gtips/reviung/reviung53/acrylic-plate/for-stacked-acrylic-case/README.md

# Stacked acrylic case  
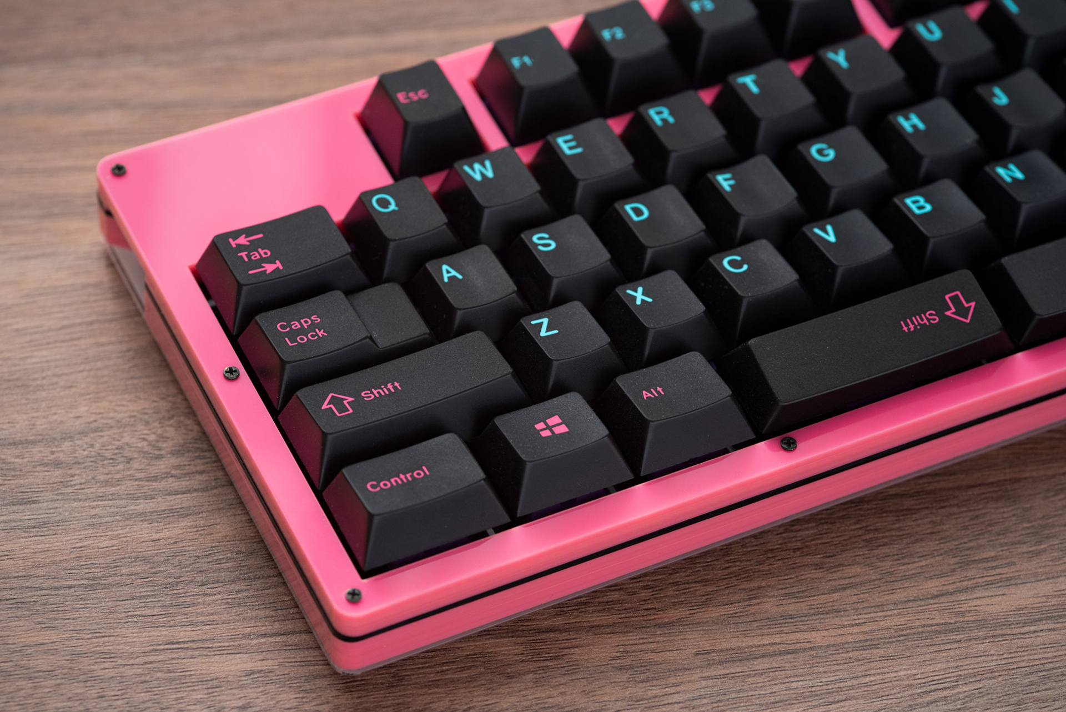
[picture p38: reviung53/image/reviung53-07.jpg]
REVIUNG53
  
  
Stacked acrylic cases.  
Includes Hi-Pro frame.  
  
Cut out the outer frame of the main PCB and install it.  
  
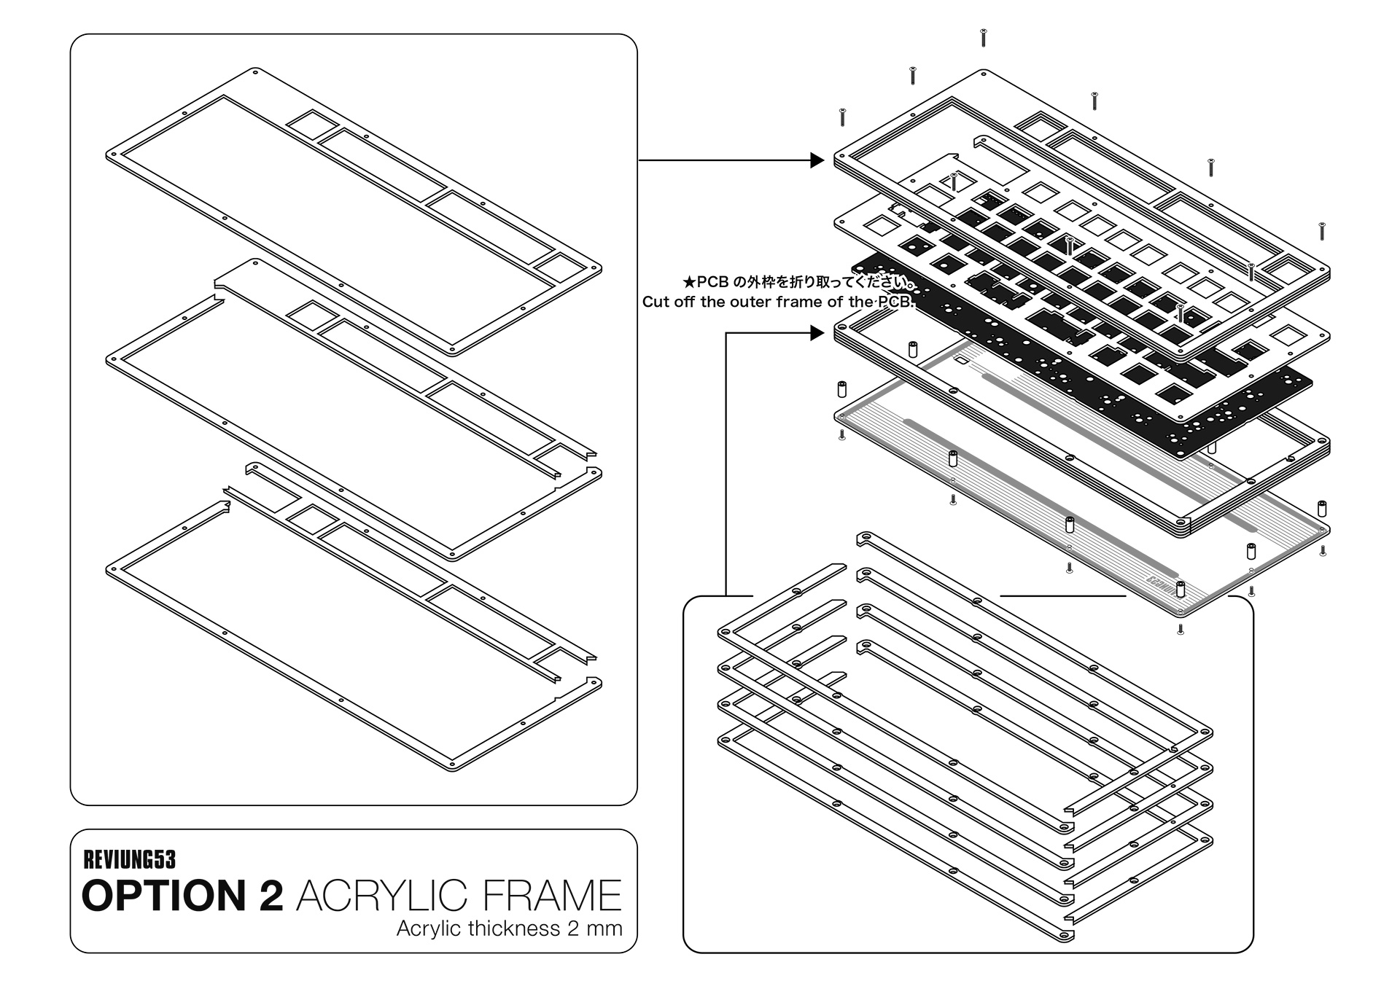
[picture p39: reviung53/acrylic-plate/for-stacked-acrylic-case/Assembly_drawing.jpg]
REVIUNG53
