gtips/reviung/reviung53/acrylic-plate/mcu-cover-ver1.0/README.md

# MCU cover  
Use this cover if you are not using the Hi-Pro frame.  

If the ProMicro pin headers come in contact, attach them with a 2 or 3mm spacer in between.
