gtips/reviung/reviung41/acrylic-plate/bottom-plate/README.md

# reviung41 bottom-plate  

Acrylic thickness is 2mm  
  
Width 253.34 mm  
Height 107.073 mm
