gtips/reviung/reviung41/acrylic-plate/top-plate/README.md

# reviung41 top-plate  

Acrylic thickness is 2mm  
  
Width 253.34 mm  
Height 101.157mm
