gtips/reviung/reviung41/acrylic-plate/lower-middle-plate/README.md

# reviung41 lower-middle-plate  

Acrylic thickness is 3mm  

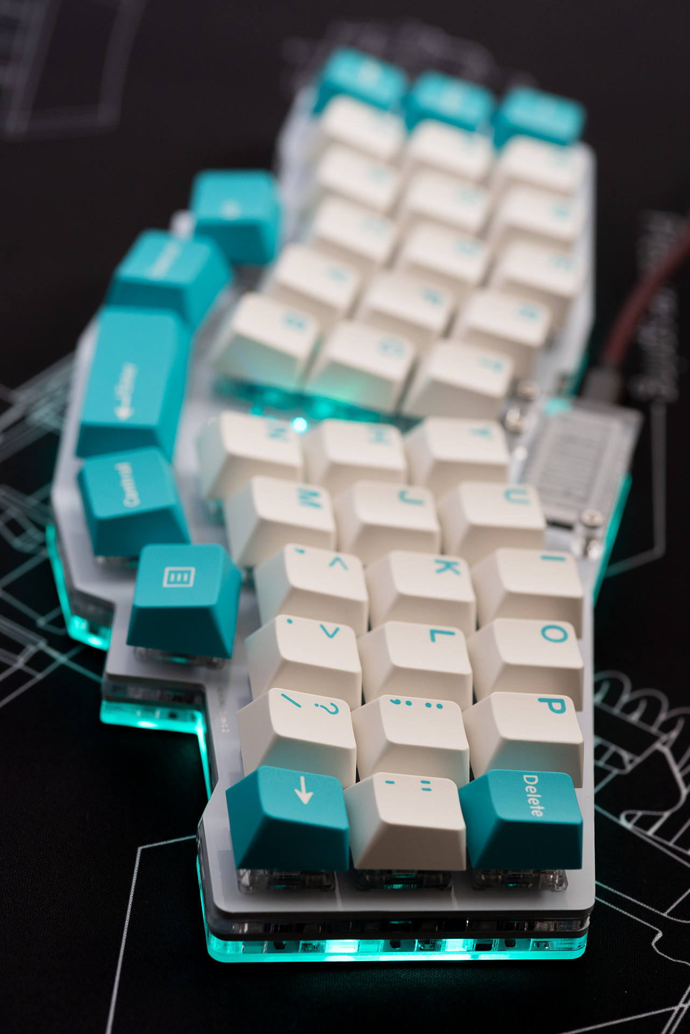
[picture p40: reviung41/image/reviung41-04.jpg]
REVIUNG41
  
<br>
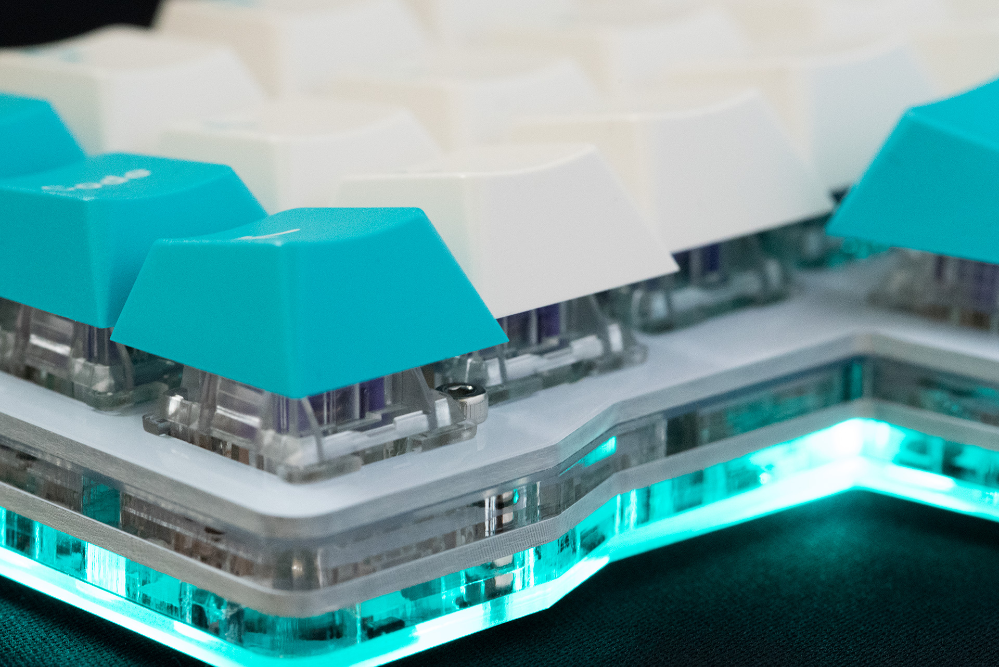
[picture p41: reviung41/image/reviung41-08.jpg]
REVIUNG41
