gtips/reviung/reviung39/acrylic-plate/upper-middle-plate/README.md

# reviung39 Upper-middle-plate
Acrylic thickness is 3mm

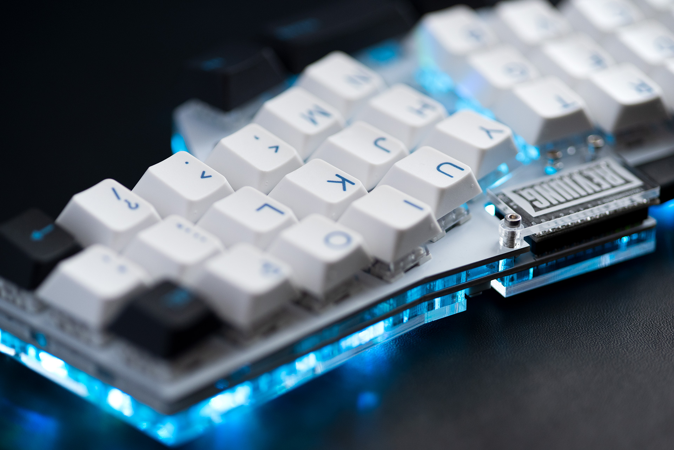
[picture p42: reviung39/image/REVIUNG39mdp-1.jpg]
REVIUNG39
  
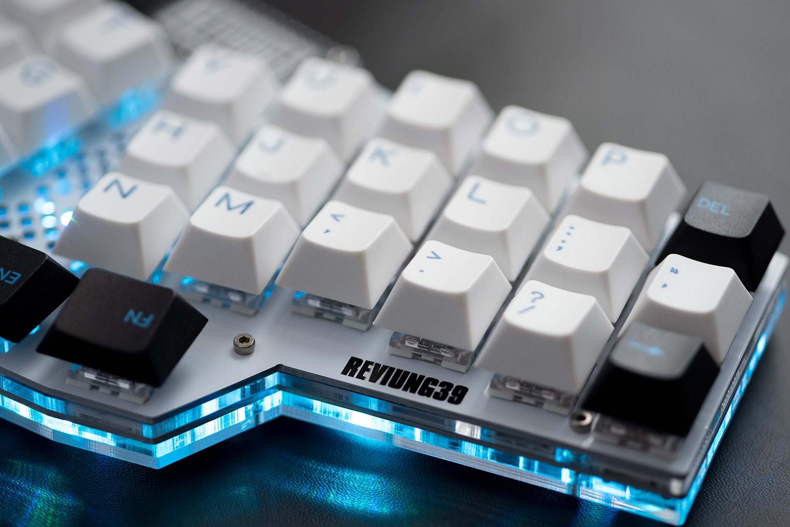
[picture p43: reviung39/image/REVIUNG39mdp-2.jpg]
REVIUNG39
  
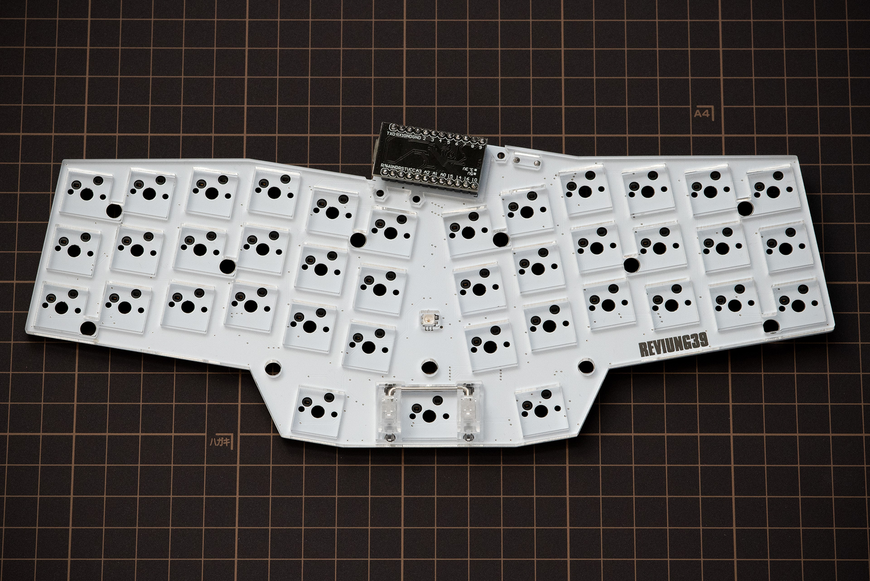
[picture p44: reviung39/image/REVIUNG39mdp-3.jpg]
REVIUNG39
  
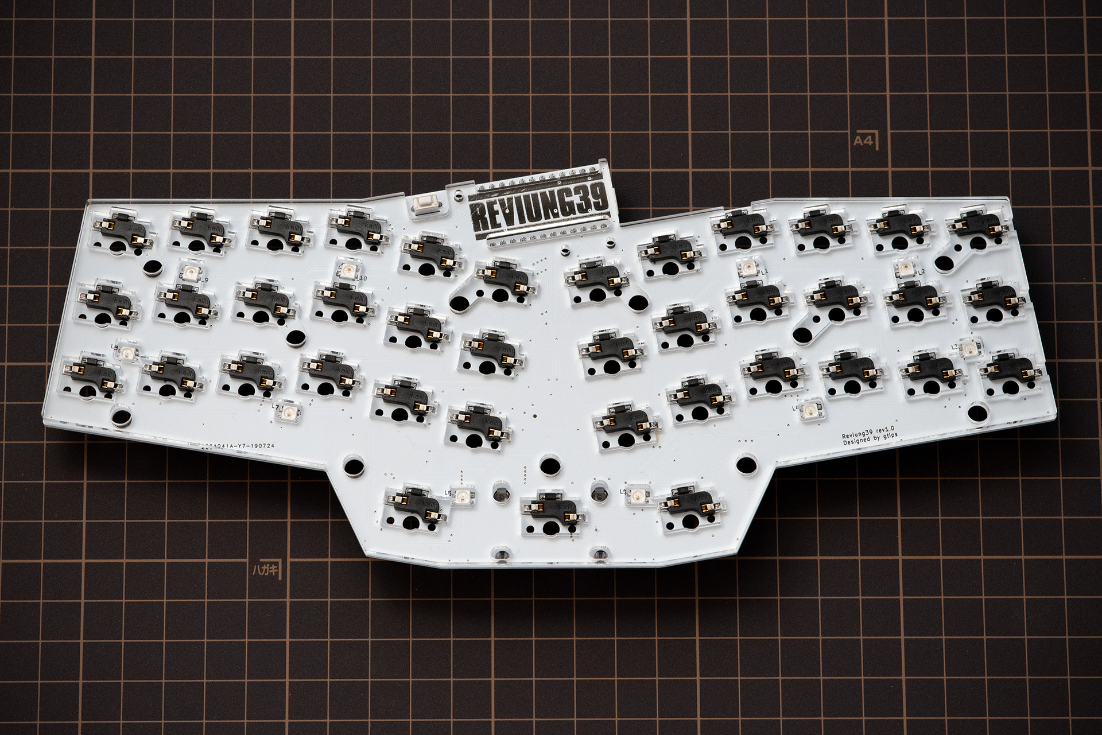
[picture p45: reviung39/image/REVIUNG39mdp-4.jpg]
REVIUNG39
  
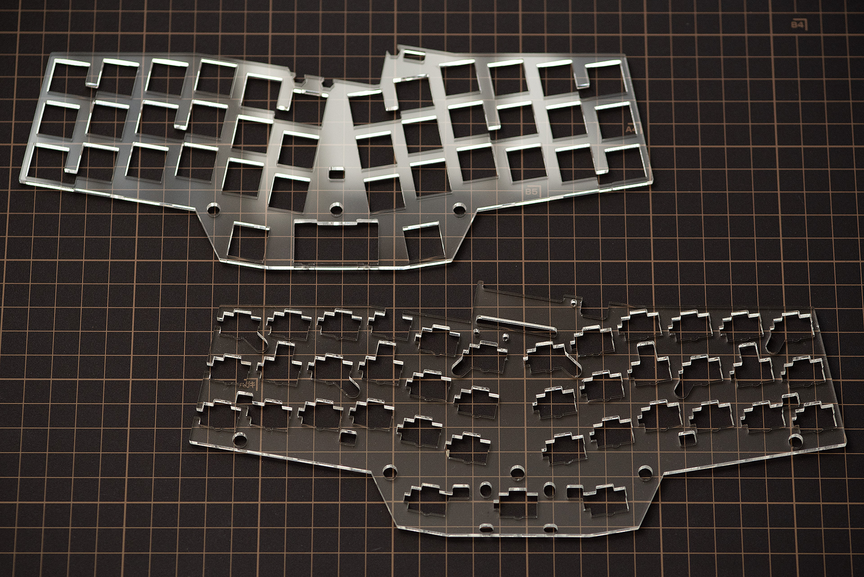
[picture p46: reviung39/image/REVIUNG39mdp-5.jpg]
REVIUNG39
