gtips/reviung/reviung39s/acrylic-plate/top-plate/README.md

# reviung39s top plate  
Acrylic thickness up to 2mm when using a stabilizer
