gtips/reviung/reviung34split/image/REVIUNG34-3.jpg

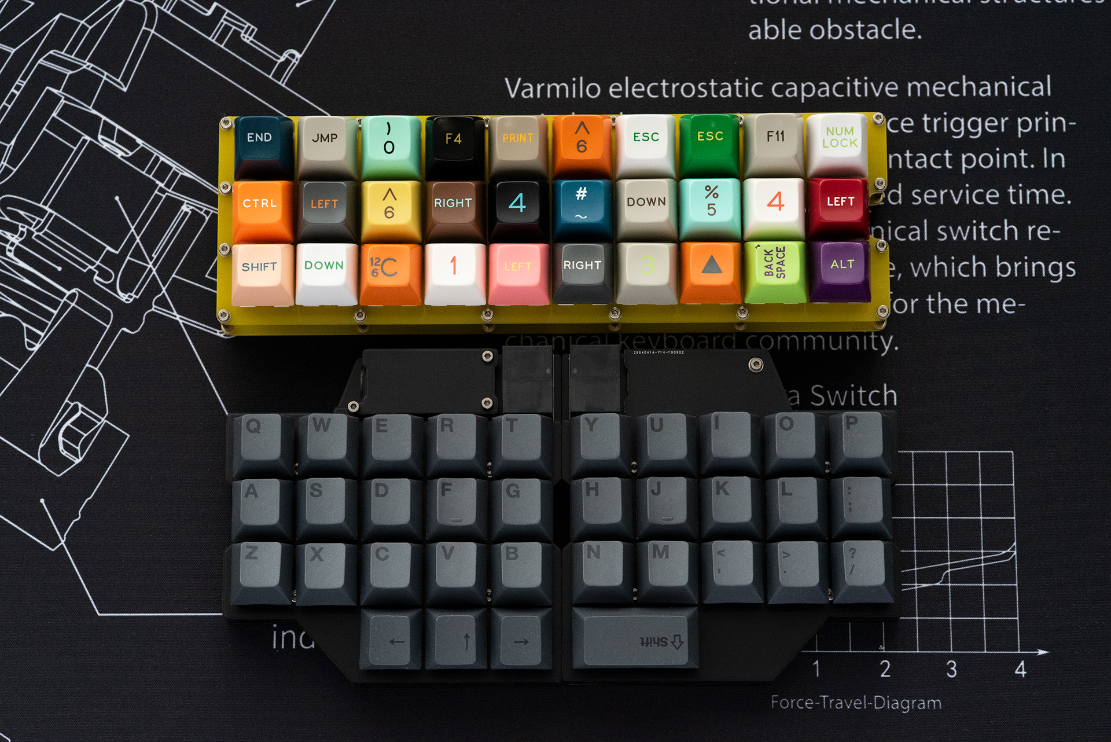
reviung34split/image/REVIUNG34-3.jpg
