gtips/reviung/reviung34split/image/REVIUNG34-4.jpg

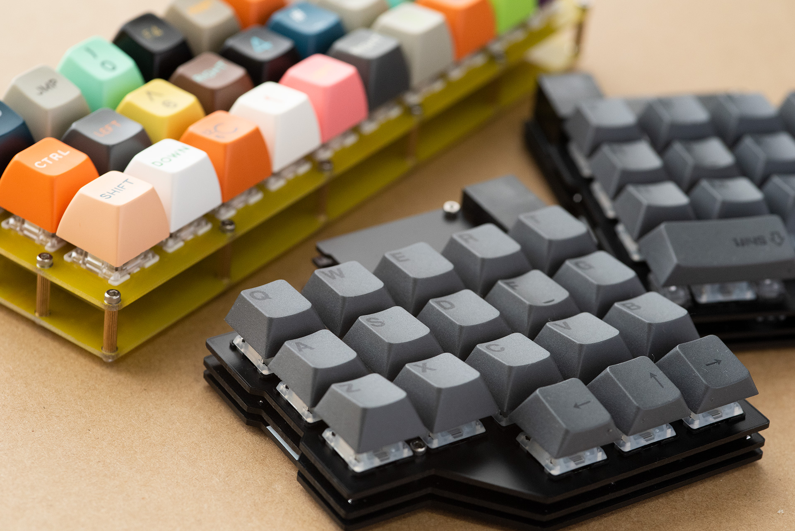
reviung34split/image/REVIUNG34-4.jpg
