gtips/reviung/reviung39s/image/REVIUNG39s-2.jpg

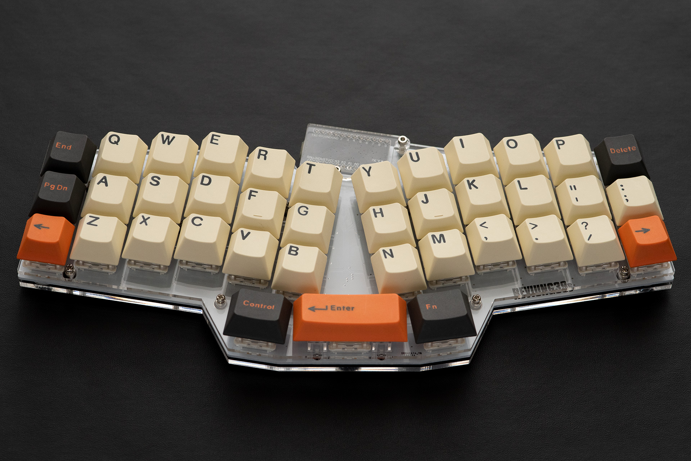
reviung39s/image/REVIUNG39s-2.jpg
