gtips/reviung/reviung39s/image/REVIUNG39s-3.jpg

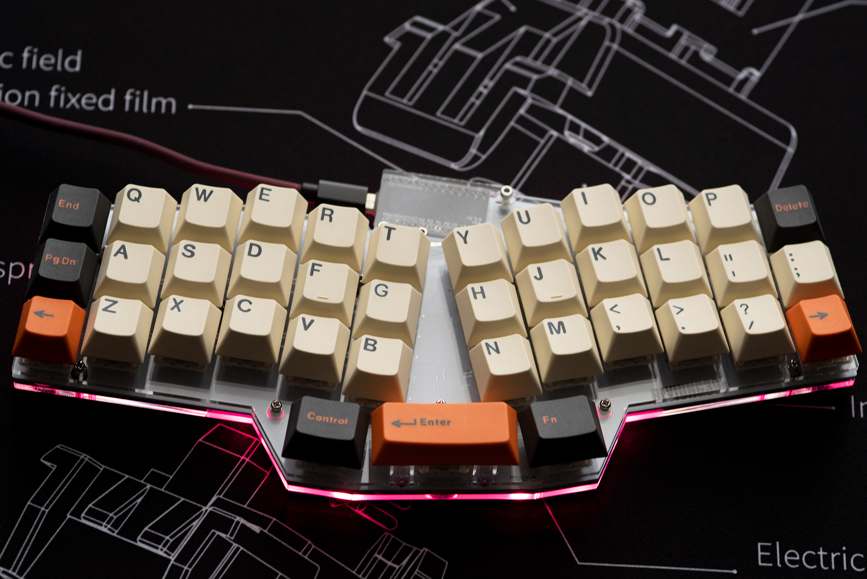
reviung39s/image/REVIUNG39s-3.jpg
