gtips/reviung/reviung39s/image/REVIUNG39s-4.jpg

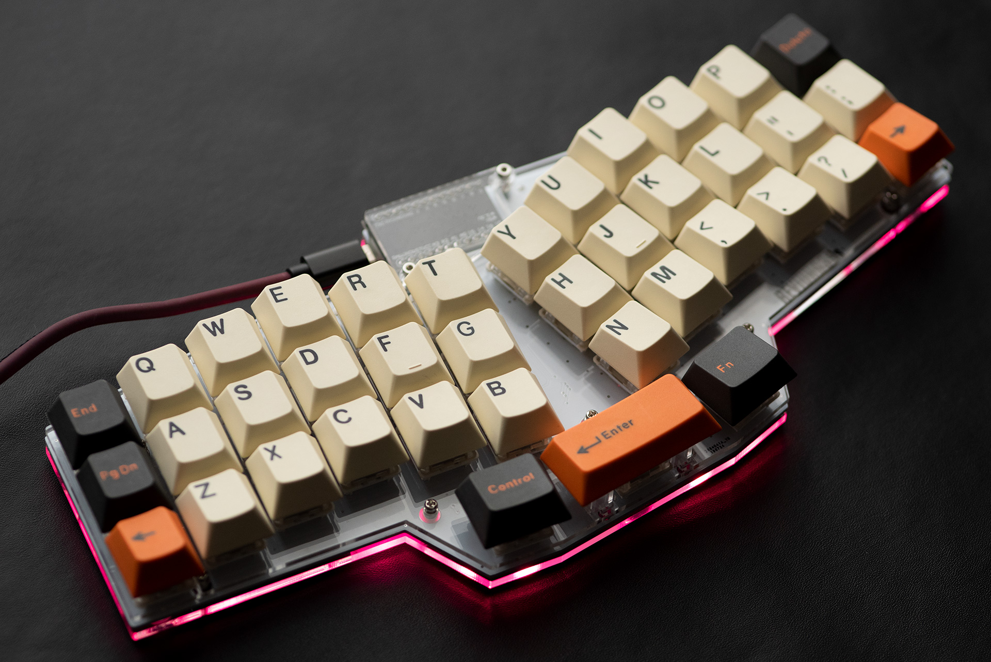
reviung39s/image/REVIUNG39s-4.jpg
