gtips/reviung/reviung41/image/reviung41-05.jpg

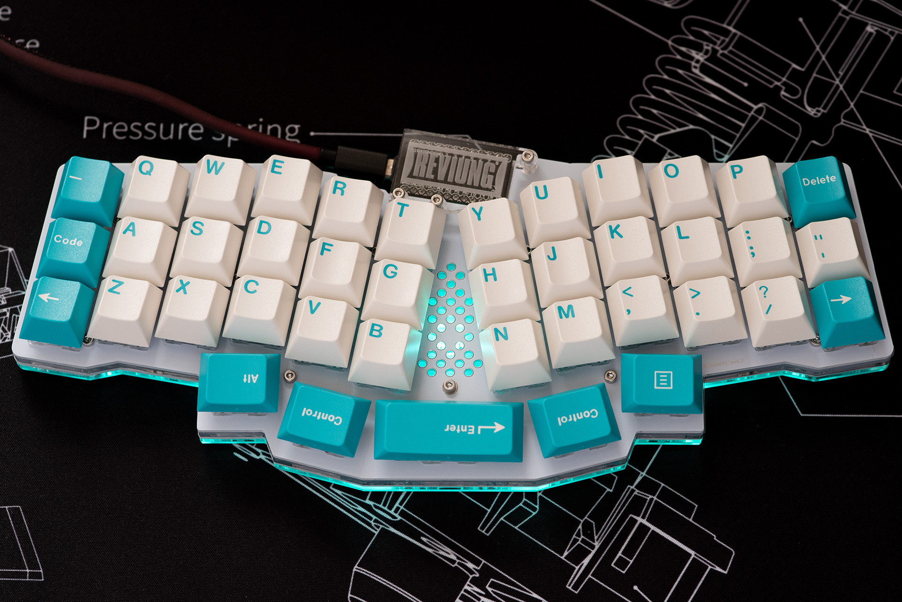
reviung41/image/reviung41-05.jpg
