gtips/reviung/reviung41/image/reviung41-06.jpg

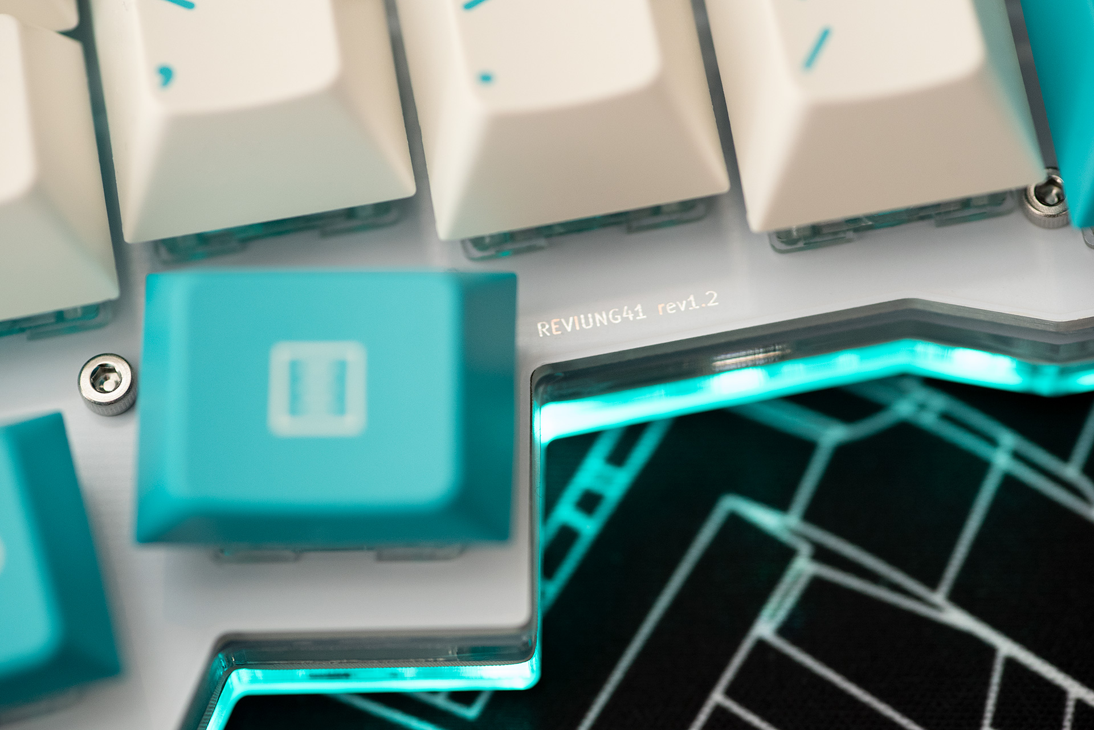
reviung41/image/reviung41-06.jpg
