gtips/reviung/reviung41/image/reviung41-07.jpg

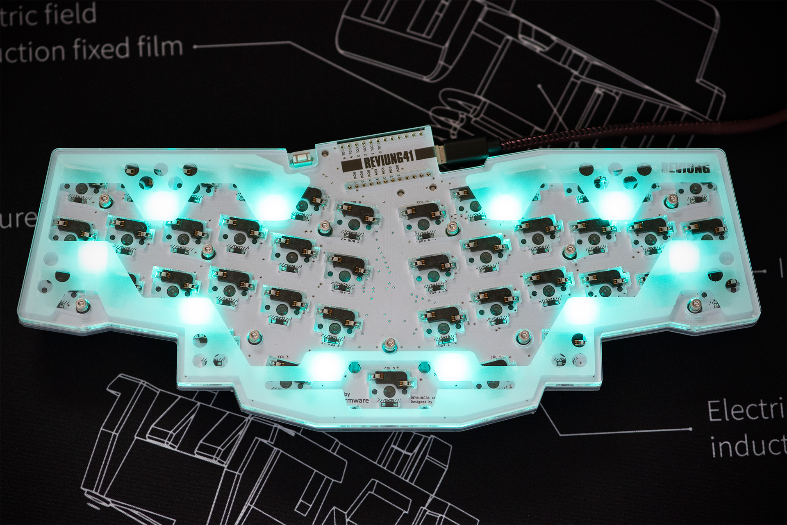
reviung41/image/reviung41-07.jpg
