gtips/reviung/reviung41/image/REVIUNG41-prototype.jpg

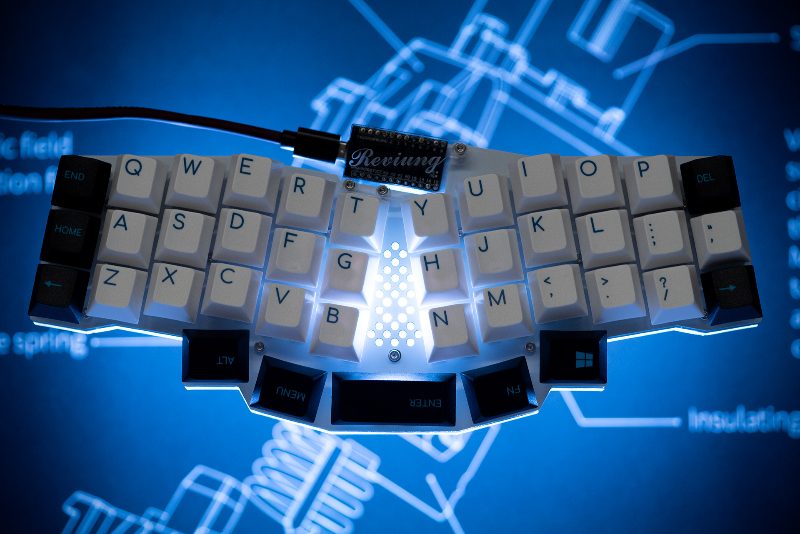
reviung41/image/REVIUNG41-prototype.jpg
