gtips/reviung/reviung46/acrylic/REVIUNG46_acrylic_ver1_1/REVIUNG46_acrylic_ver1_1_correct_dimension.jpg

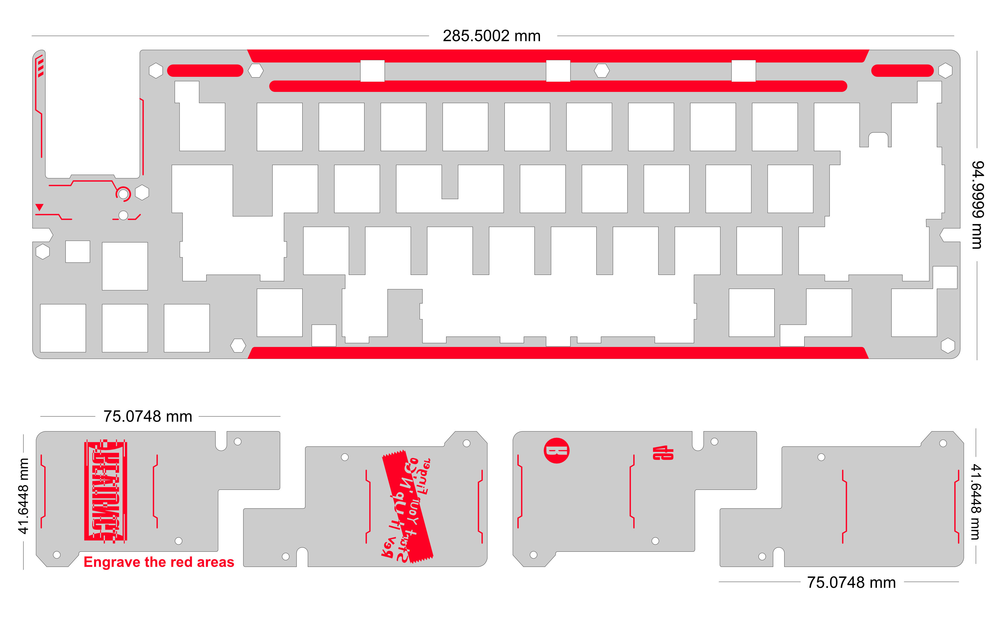
reviung46/acrylic/REVIUNG46_acrylic_ver1_1/REVIUNG46_acrylic_ver1_1_correct_dimension.jpg
