gtips/reviung/reviung46/image/reviung46-01.jpg

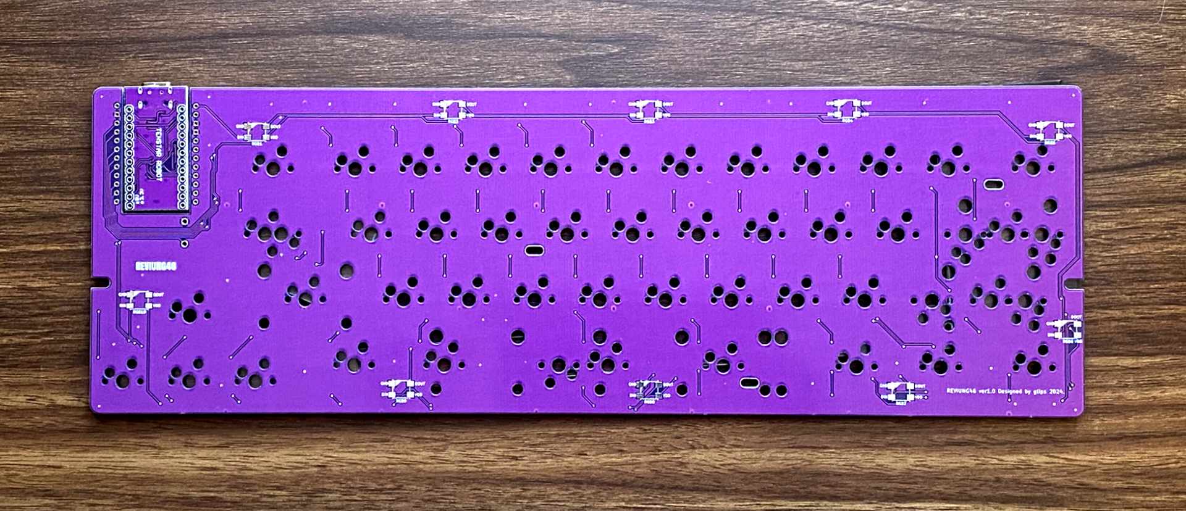
reviung46/image/reviung46-01.jpg
