gtips/reviung/reviung53/image/reviung53-06.jpg

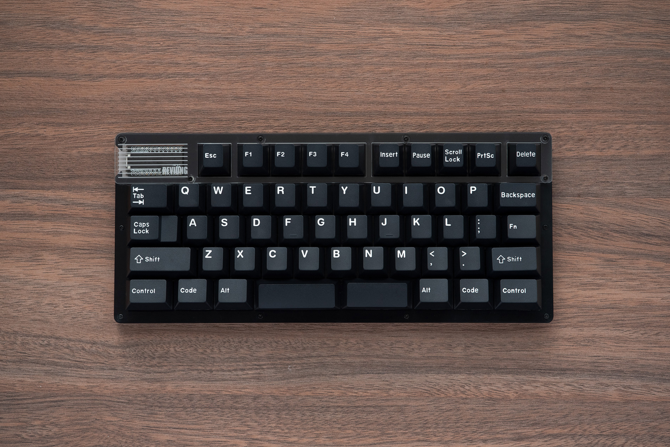
reviung53/image/reviung53-06.jpg
