gtips/reviung/reviung53/acrylic-plate/bottom-plate-ver1.0/reviung53-bottom-plate-2mm-ver1.0.pdf

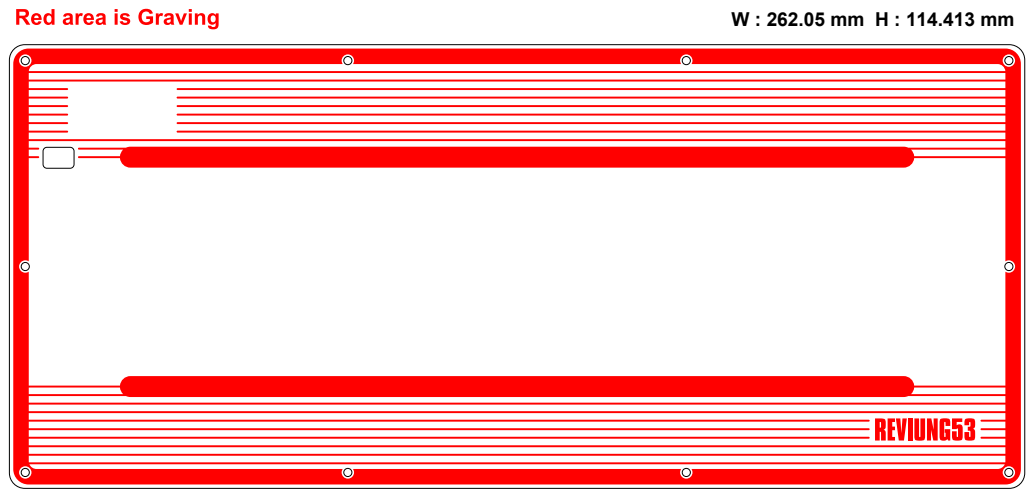
[picture p88: page 1]
