gtips/reviung/reviung5/pcb/ver1.0/circuit_diagram.pdf

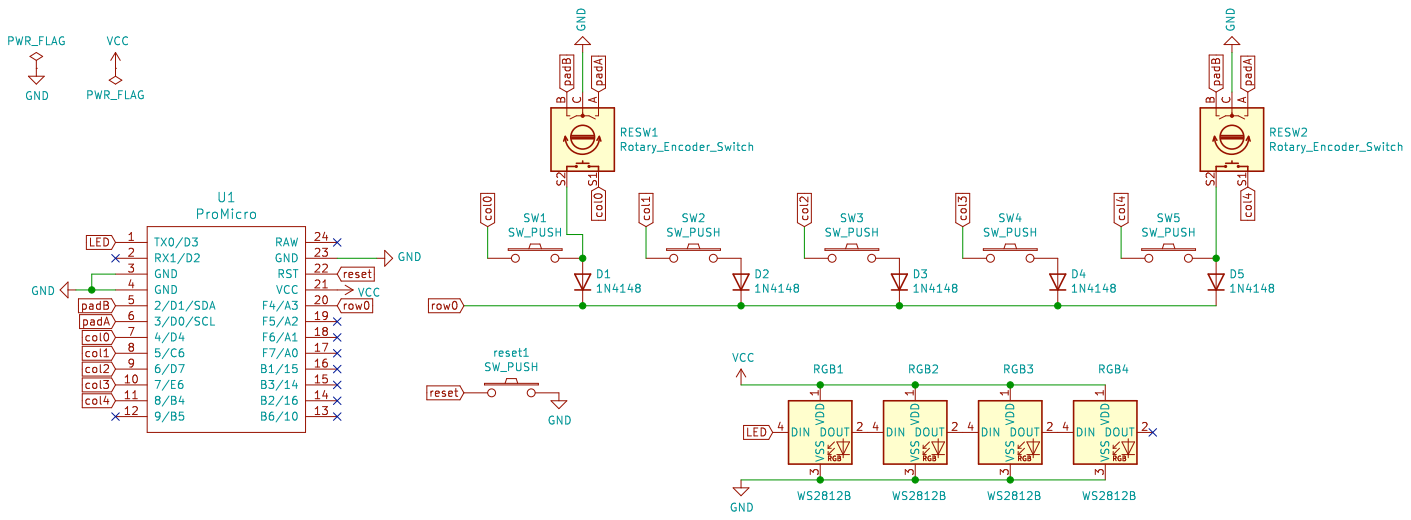
[picture p89: page 1]
