gtips/reviung/reviung41/acrylic-plate/top-plate/reviung41-top-plate.pdf

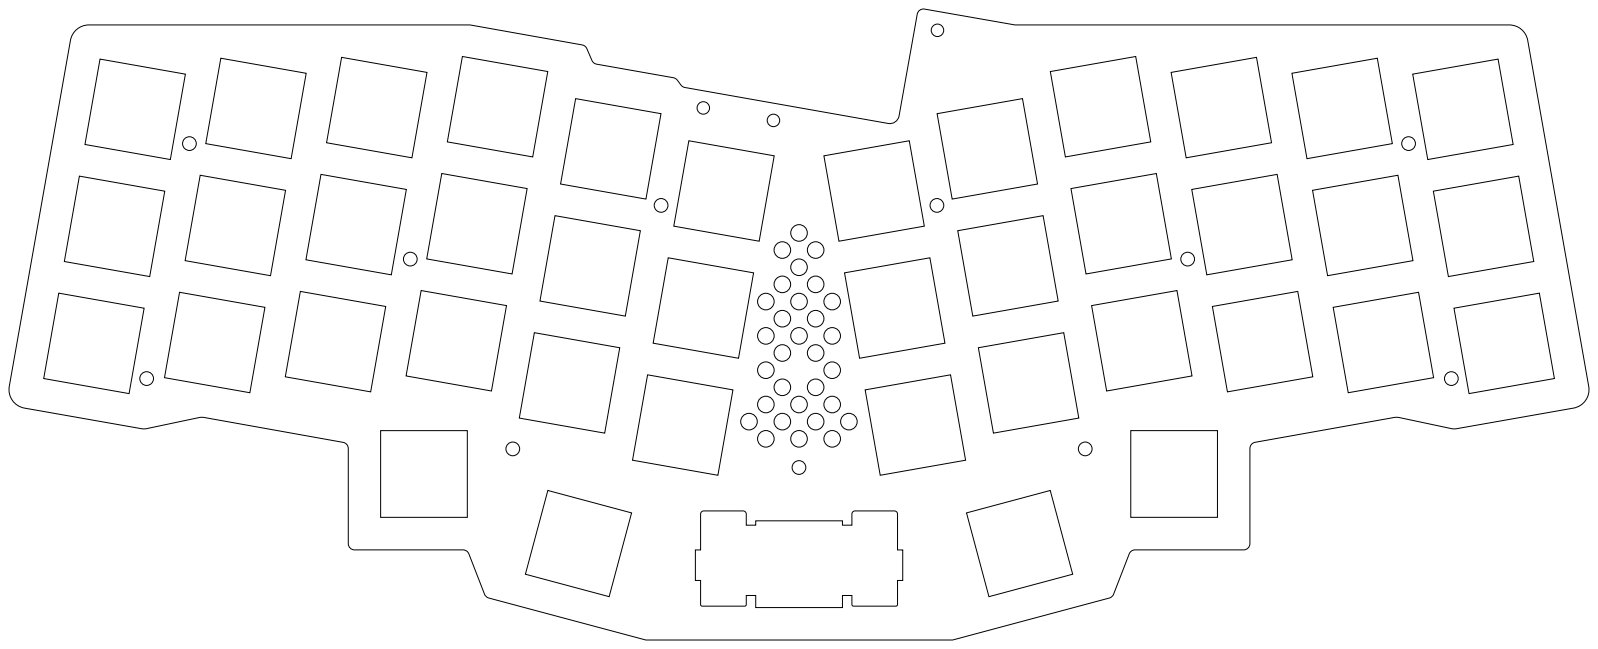
[picture p90: page 1]
