gtips/reviung/reviung34split_Mk-II/pcb/main-pcb/reviung34-split-L.pdf

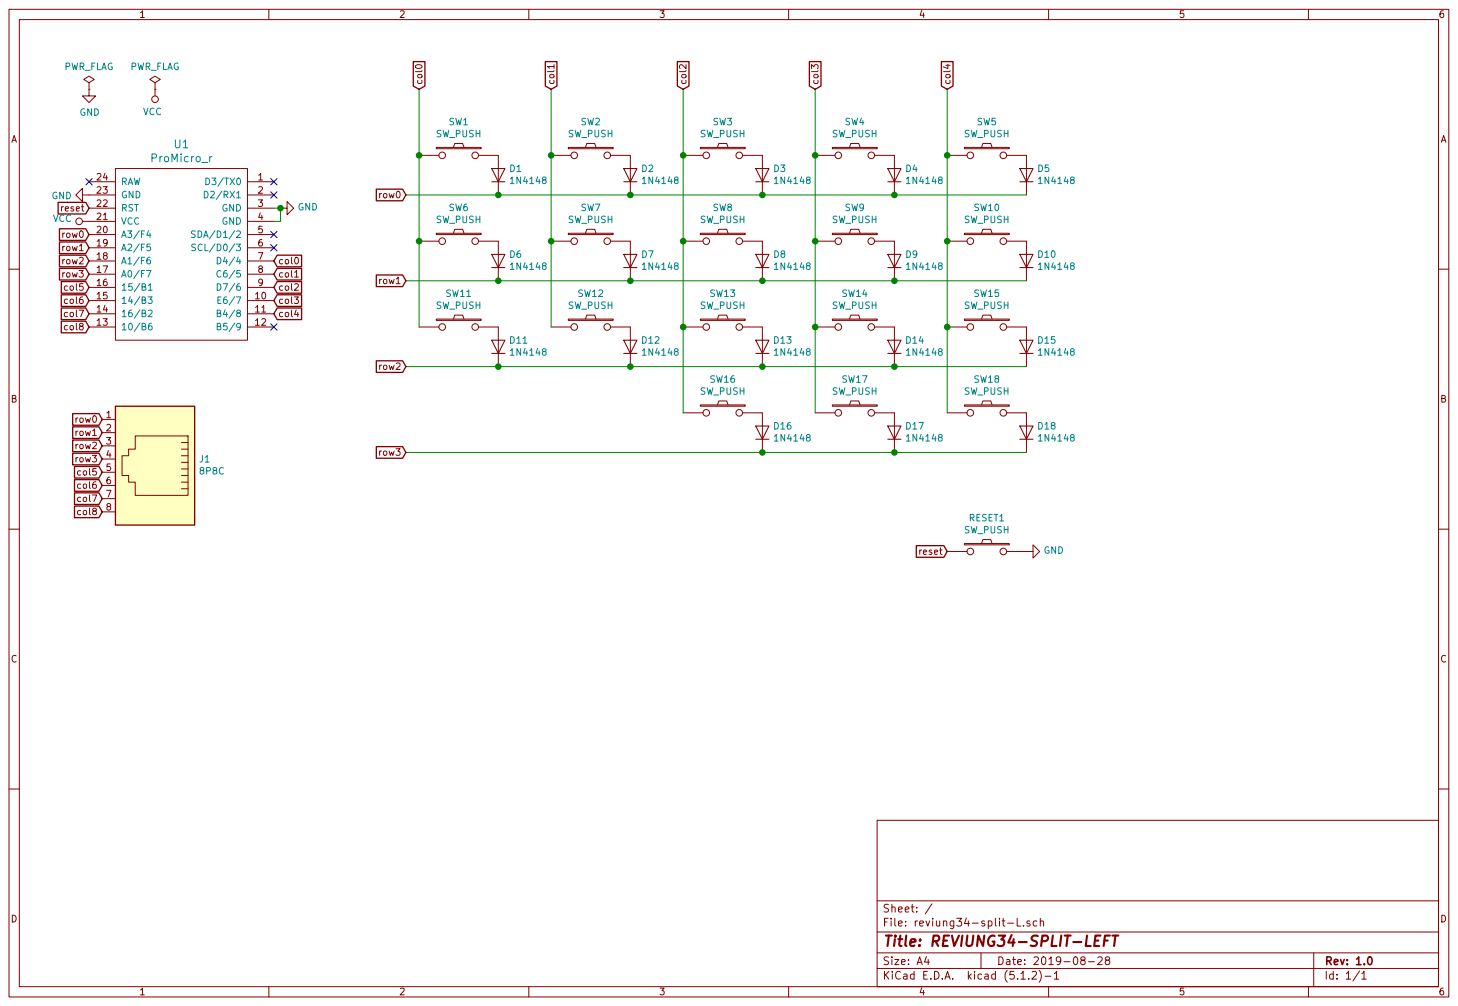
[picture p91: page 1]

File: reviung34-split-L.sch Sheet: /
Id: 1/1 Title: REVIUNG34-SPLIT-LEFT
