gtips/reviung/reviung46/pcb/reviung46_ver1_1/reviung46/R46ver1.1PCB.pdf

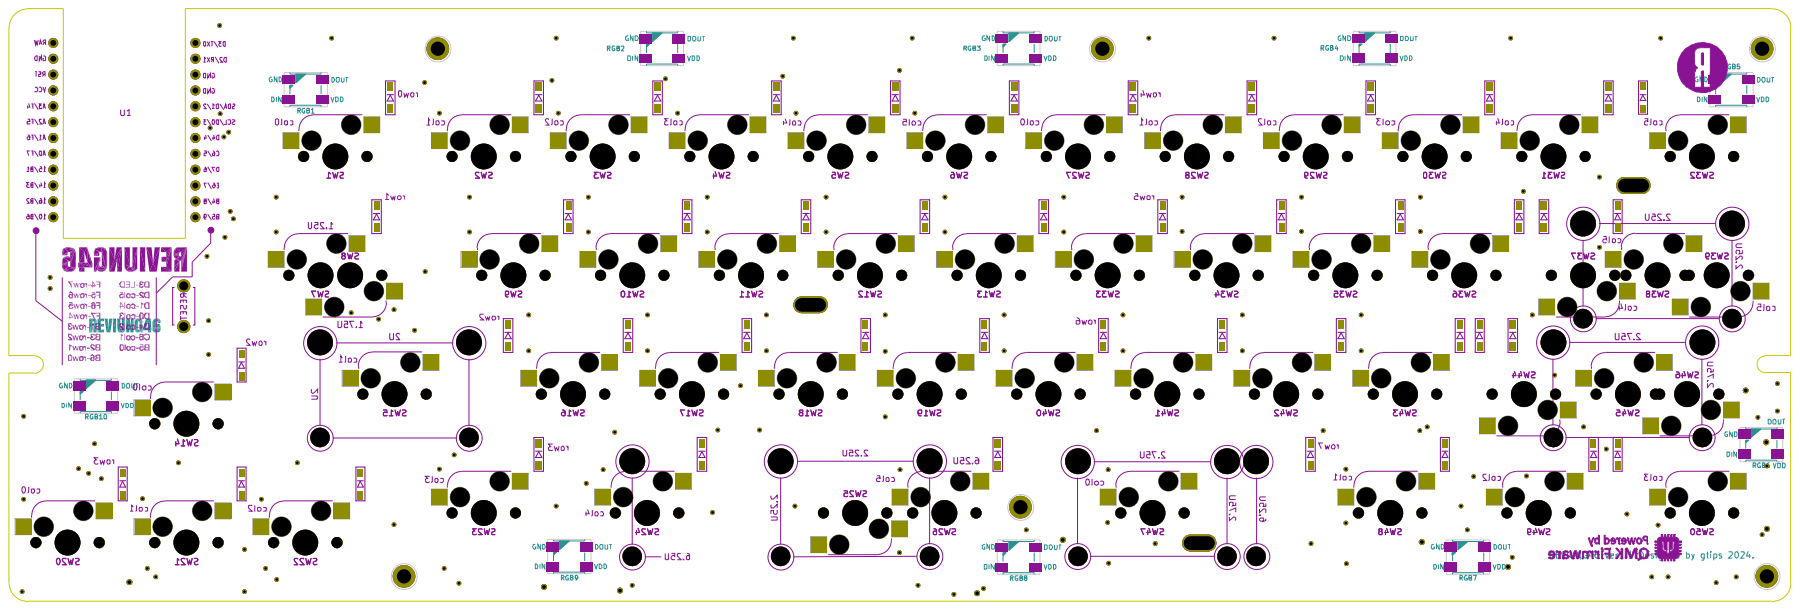
[picture p92: page 1]
