gtips/reviung/reviung46/pcb/reviung46_ver1_1/reviung46/reviung46.pdf

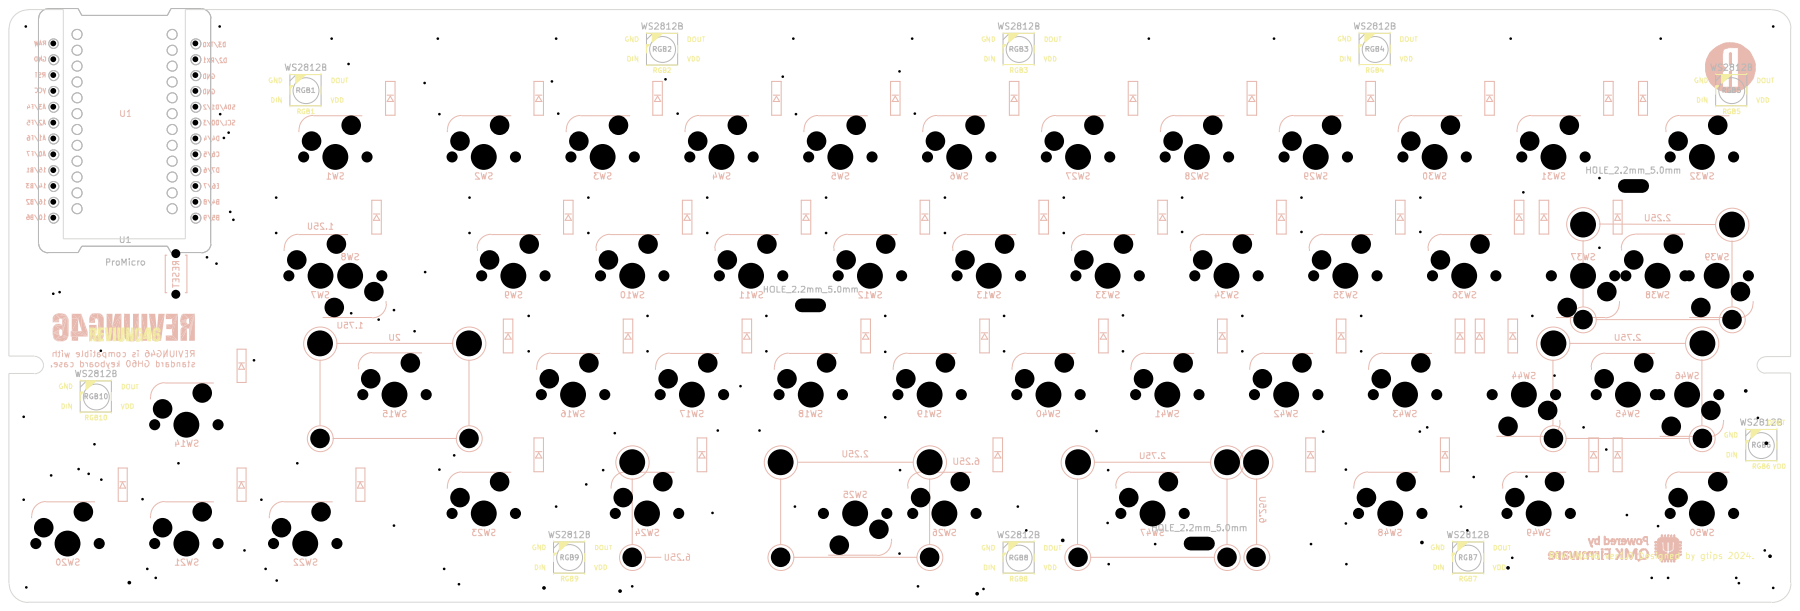
[picture p93: page 1]
