gtips/reviung/reviung41/acrylic-plate/bottom-plate/ver1.1/reviung41-bottom-plate-ver1.1.pdf

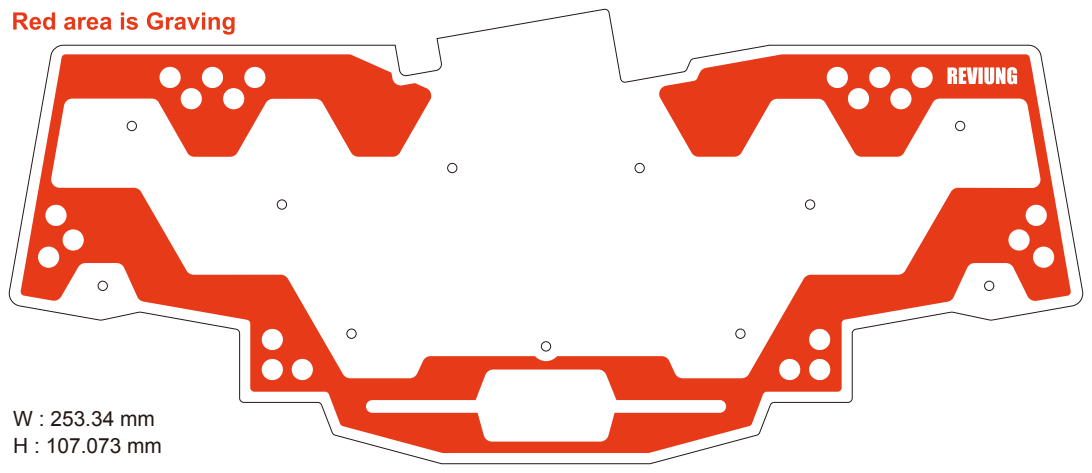
[picture p94: page 1]
