gtips/reviung/reviung41/acrylic-plate/lower-middle-plate/ver1.1/reviung41-lower-middle-plate-ver1.1.pdf

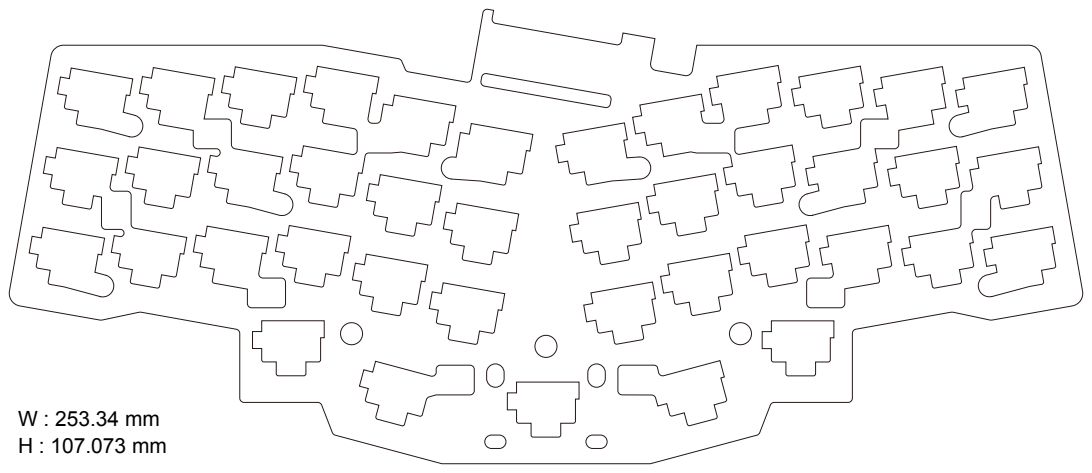
[picture p95: page 1]
