gtips/reviung/reviung34/acrylic-plate/bottom-plate/ver1.1/reviung34-bottom-plate-2mm-ver1.1.pdf

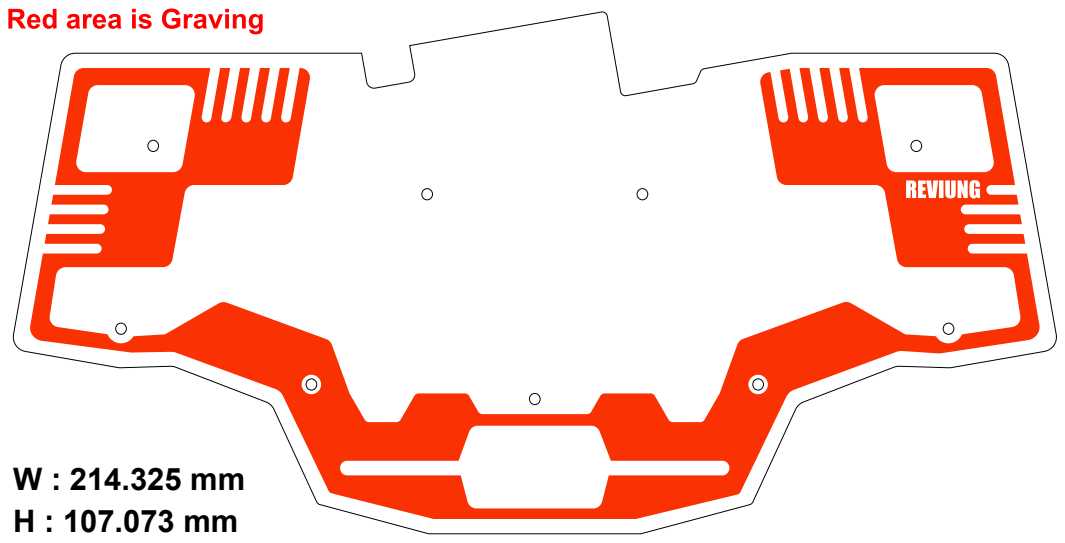
[picture p96: page 1]
