gtips/reviung/reviung34/acrylic-plate/lower-middle-plate/ver1.1/r34-lower-middle-3mm-ver1.1-TP.pdf

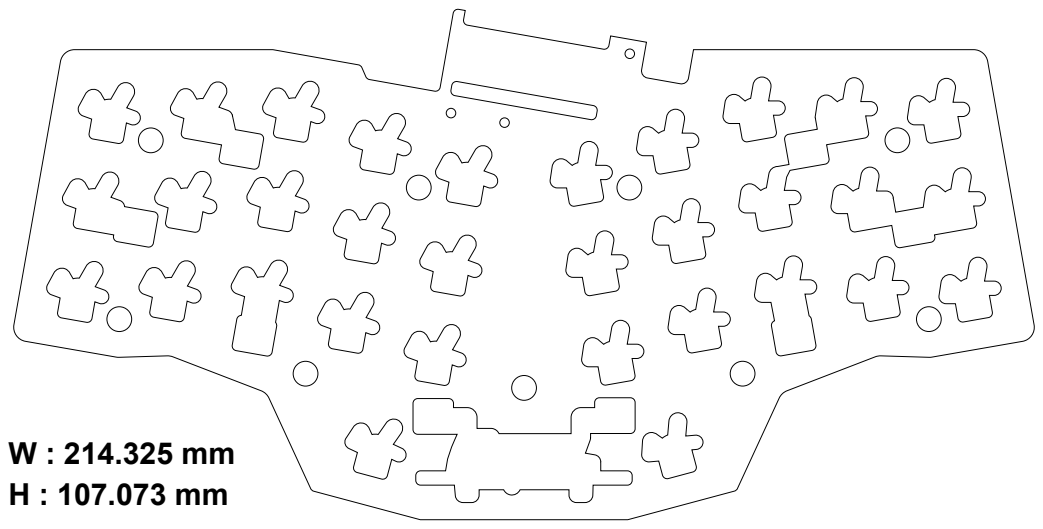
[picture p97: page 1]
