gtips/reviung/reviung39_Mk-II/acrylic-plate/bottom-plate/ver1.3/reviung39MkII-bottom-plate-2mm-ver1.3.pdf

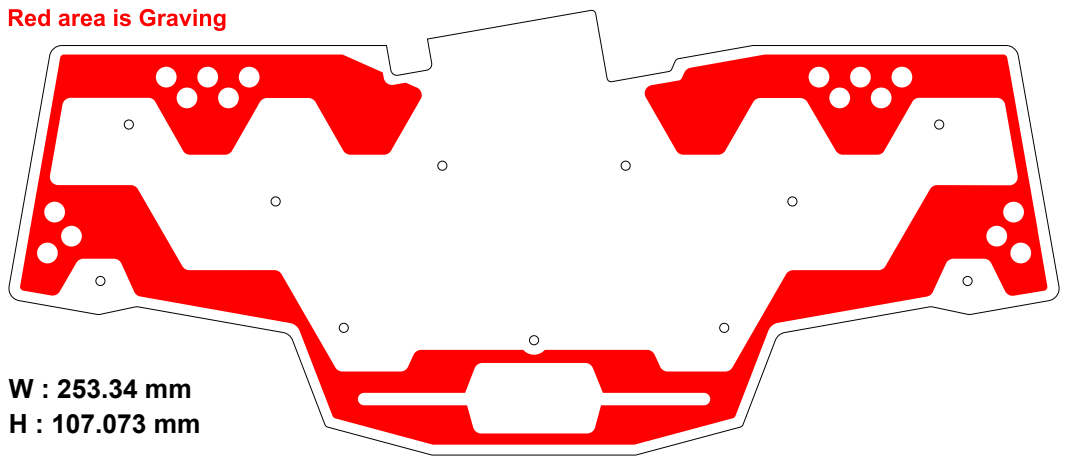
[picture p98: page 1]
