gtips/reviung/reviung5/acrylic-plate/ProMicro-cover/pdf/reviung39-ProMicro-cover-marked-A.pdf

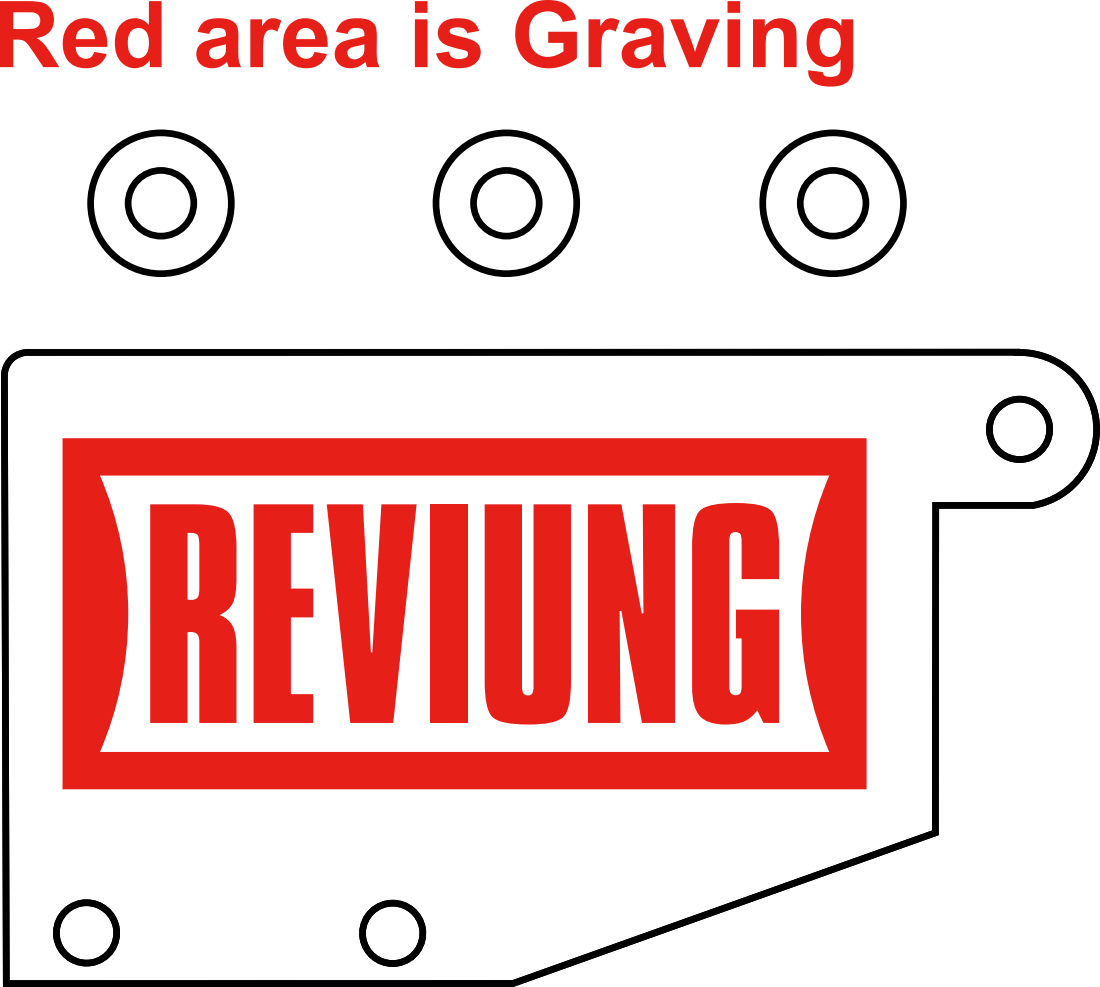
[picture p99: page 1]
