gtips/reviung/reviung5/acrylic-plate/ProMicro-cover/pdf/reviung39-ProMicro-cover-marked-B.pdf

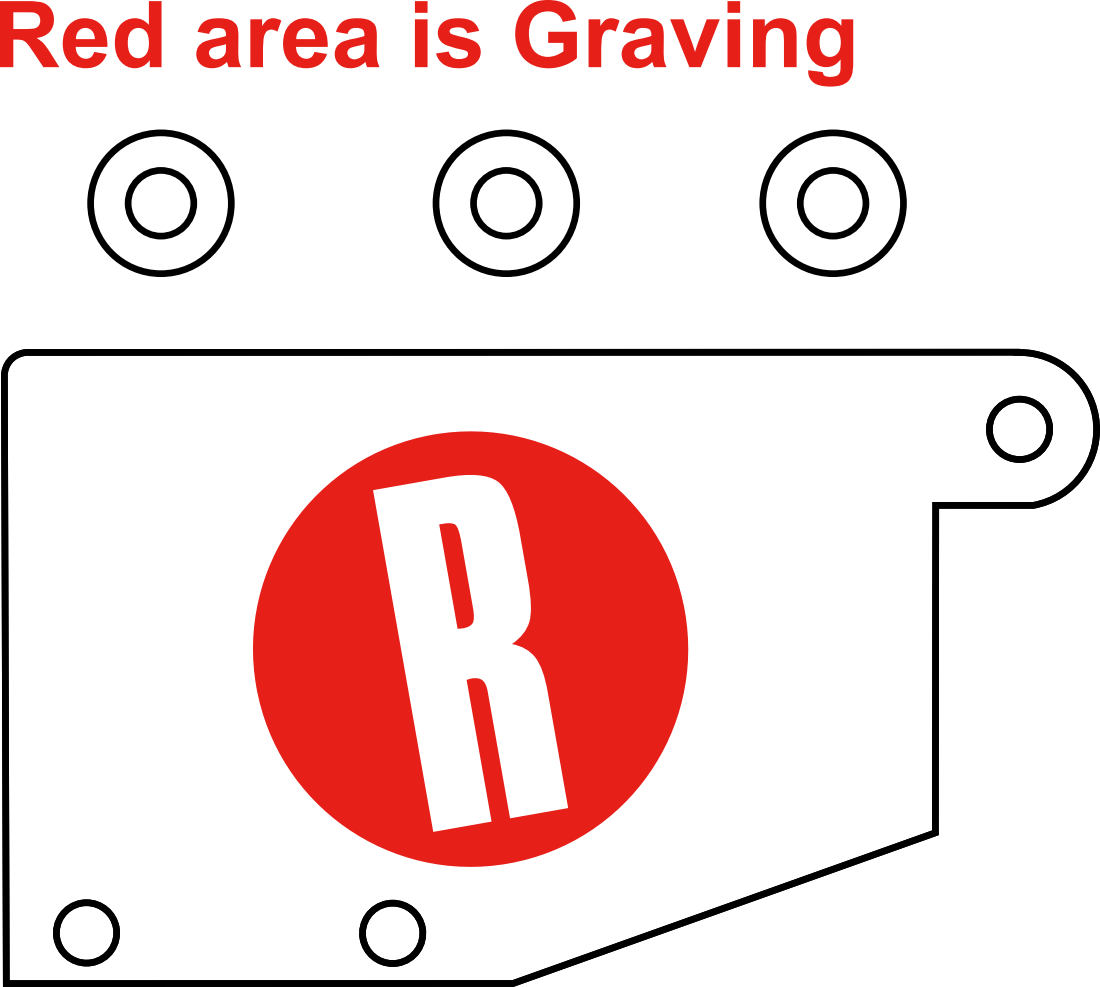
[picture p100: page 1]
