gtips/reviung/reviung5/acrylic-plate/ProMicro-cover/pdf/reviung39-ProMicro-cover-marked-C.pdf

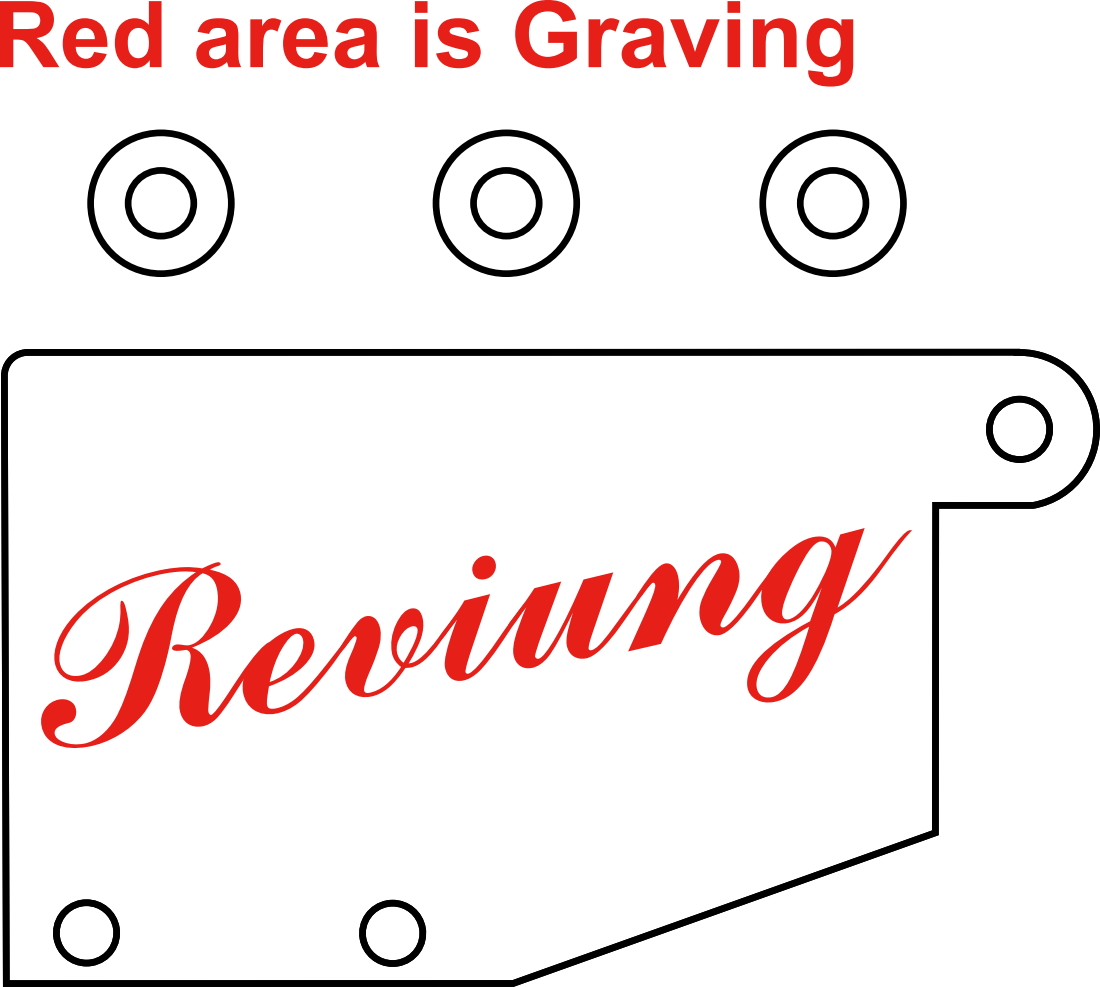
[picture p101: page 1]
