gtips/reviung/reviung5/acrylic-plate/ProMicro-cover/pdf/reviung39-ProMicro-cover.pdf

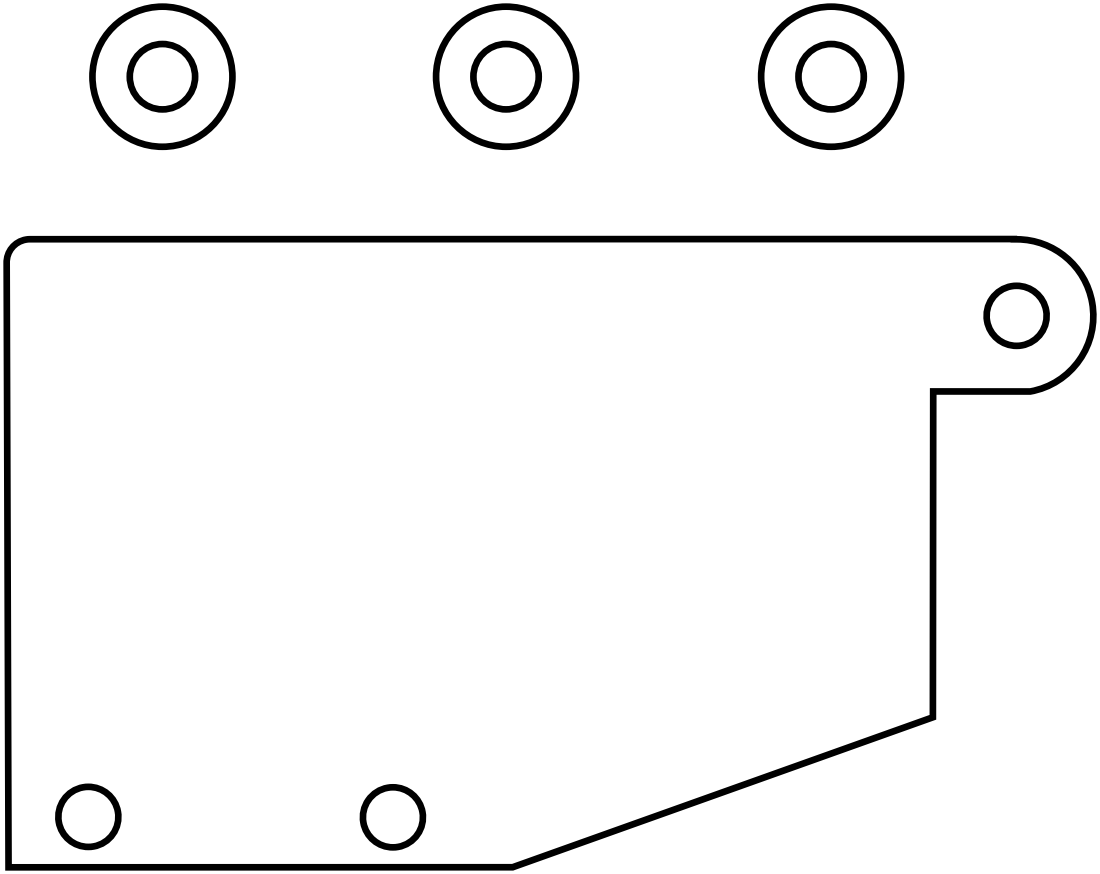
[picture p102: page 1]
