gtips/reviung/reviung41/acrylic-plate/upper-middle-plate/ver1.1/for-transparent/reviung41-upper-middle-plate-ver1.1.pdf

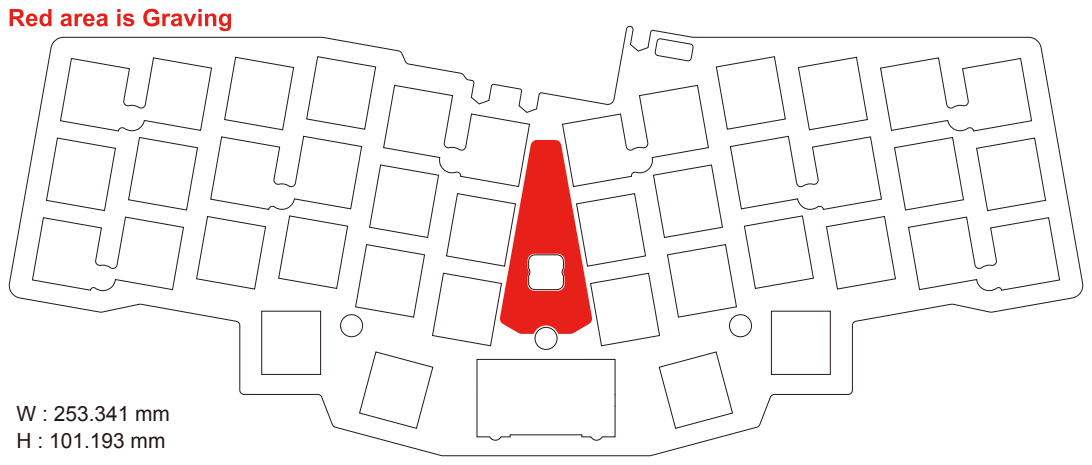
[picture p103: page 1]
