gtips/reviung/reviung34/acrylic-plate/upper-middle-plate/for-opaque/ver1.1/r34-upper-middle-3mm-ver1.1-OP.pdf

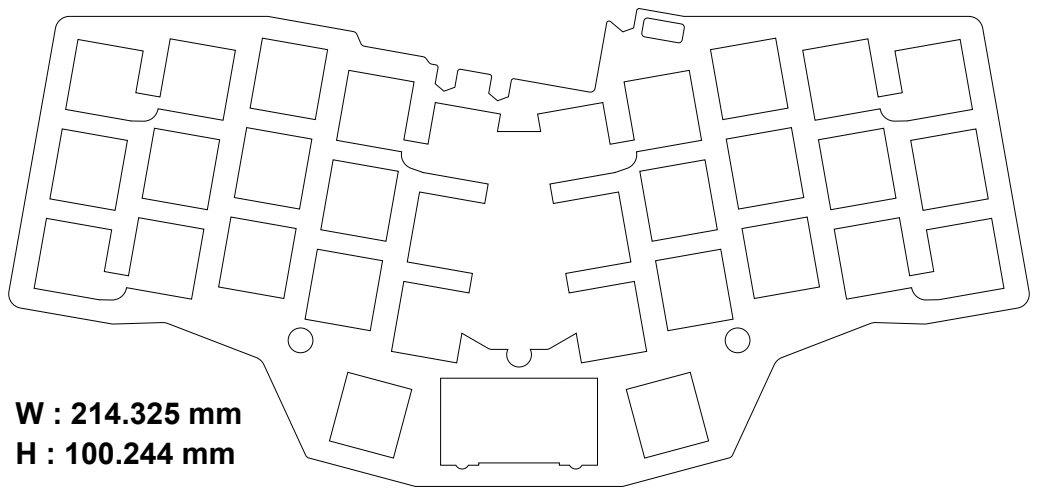
[picture p104: page 1]
