gtips/reviung/reviung34/acrylic-plate/upper-middle-plate/for-transparent/ver1.1/r34-upper-middle-3mm-ver1.1-TP.pdf

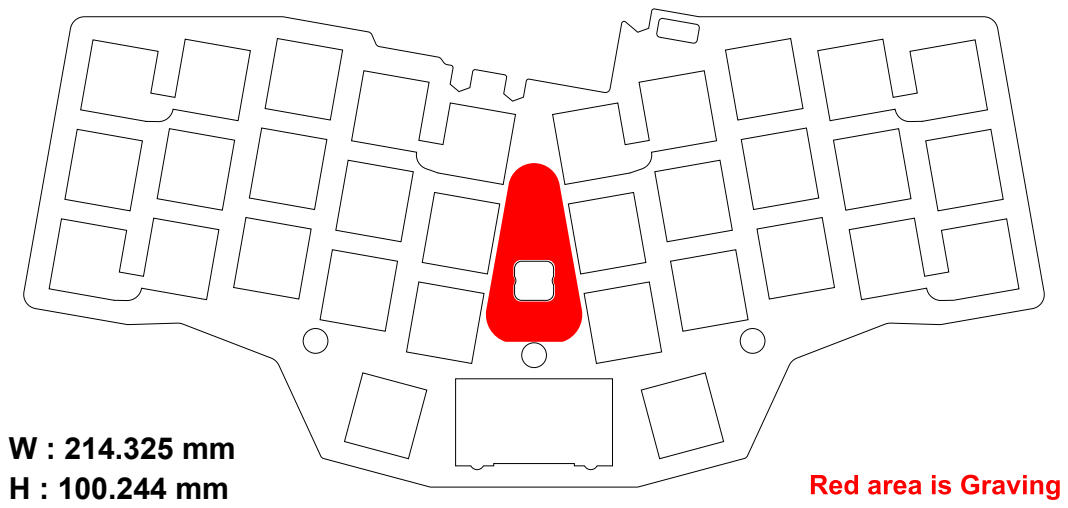
[picture p105: page 1]
