gtips/reviung/reviung39_Mk-II/acrylic-plate/lower-middle-plate/for-opaque/ver1.2/r39mkII-lower-middle-3mm-ver1.2-OP.pdf

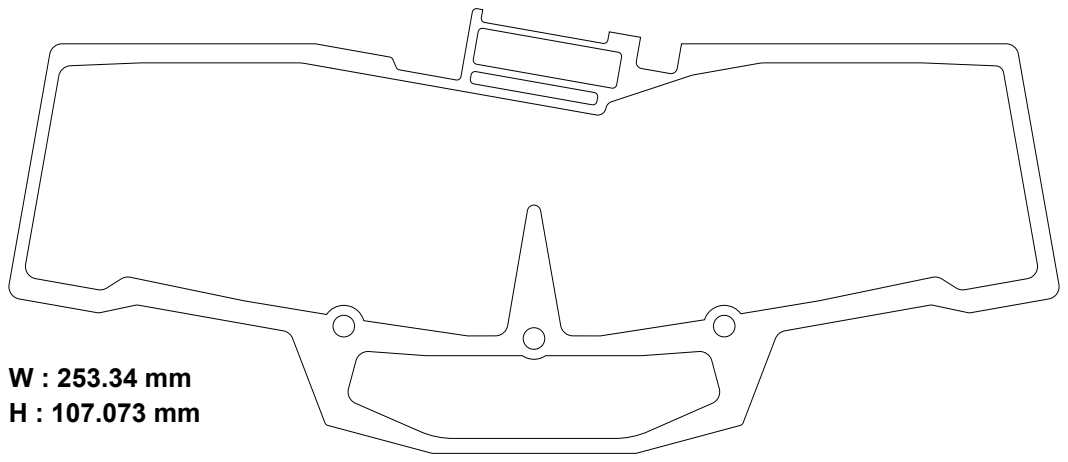
[picture p106: page 1]
