gtips/reviung/reviung39_Mk-II/acrylic-plate/lower-middle-plate/for-transparent/ver1.2/r39mkII-lower-middle-3mm-ver1.2-TP.pdf

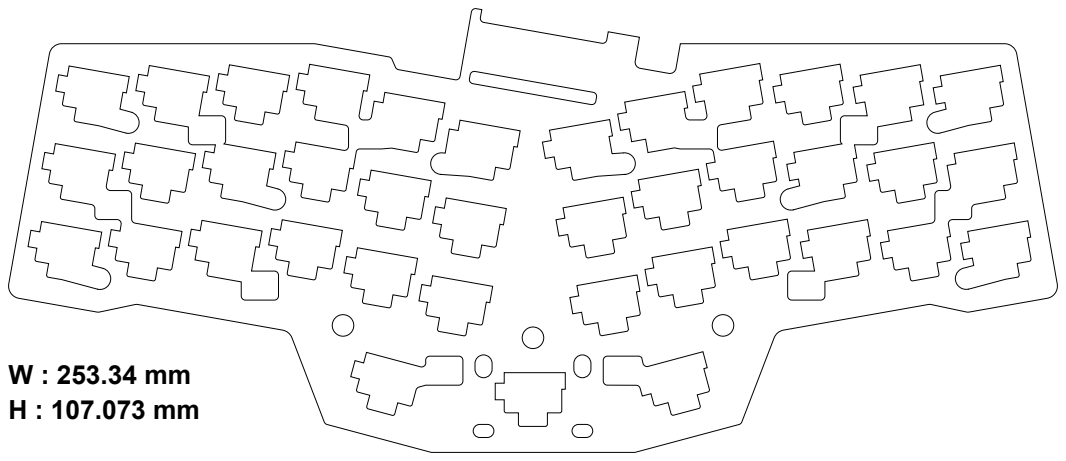
[picture p107: page 1]
