gtips/reviung/reviung39_Mk-II/acrylic-plate/upper-middle-plate/for-opaque/ver1.1/r39mkII-upper-middle-3mm-ver1.1-OP.pdf

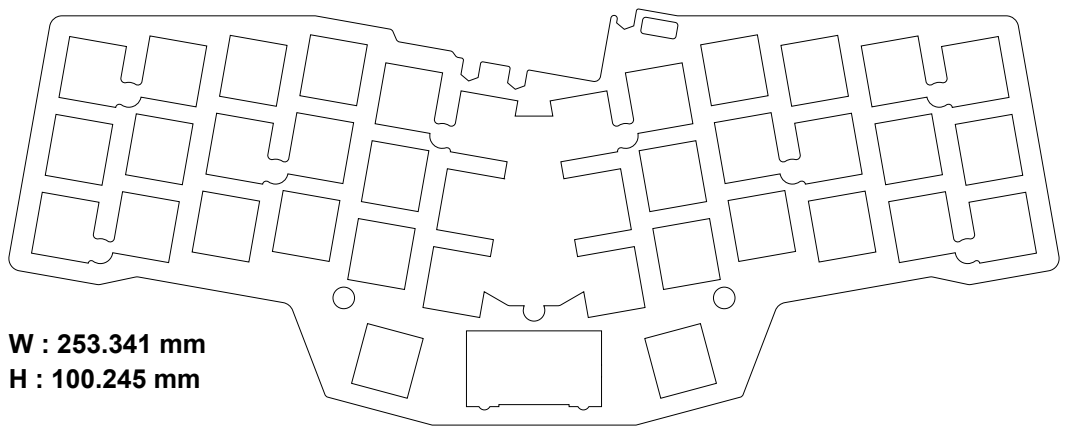
[picture p108: page 1]
