gtips/reviung/reviung39_Mk-II/acrylic-plate/upper-middle-plate/for-transparent/ver1.1/r39mkII-upper-middle-3mm-ver1.1-TP.pdf

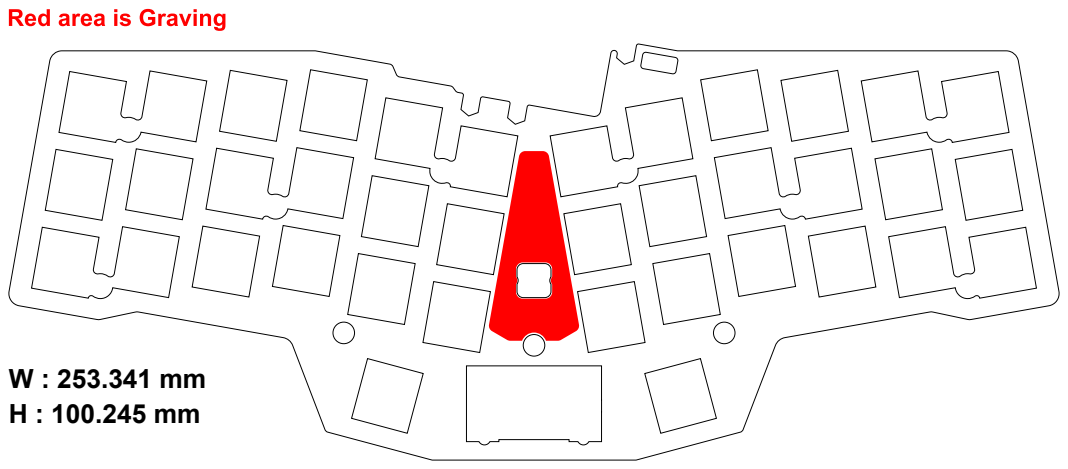
[picture p109: page 1]
