gtips/reviung/reviung41/acrylic-plate/upper-middle-plate/ver1.1/for-opaque/ver1.0/r41-upper-middle-3mm-ver1.0-OP.pdf

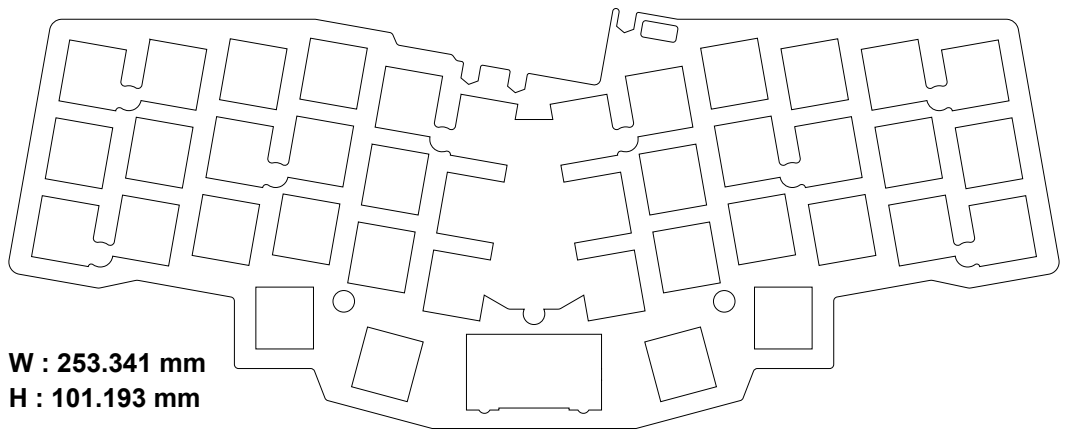
[picture p110: page 1]
