gtips/reviung/reviung41/pcb/ver1.3/circuit_diagram.pdf

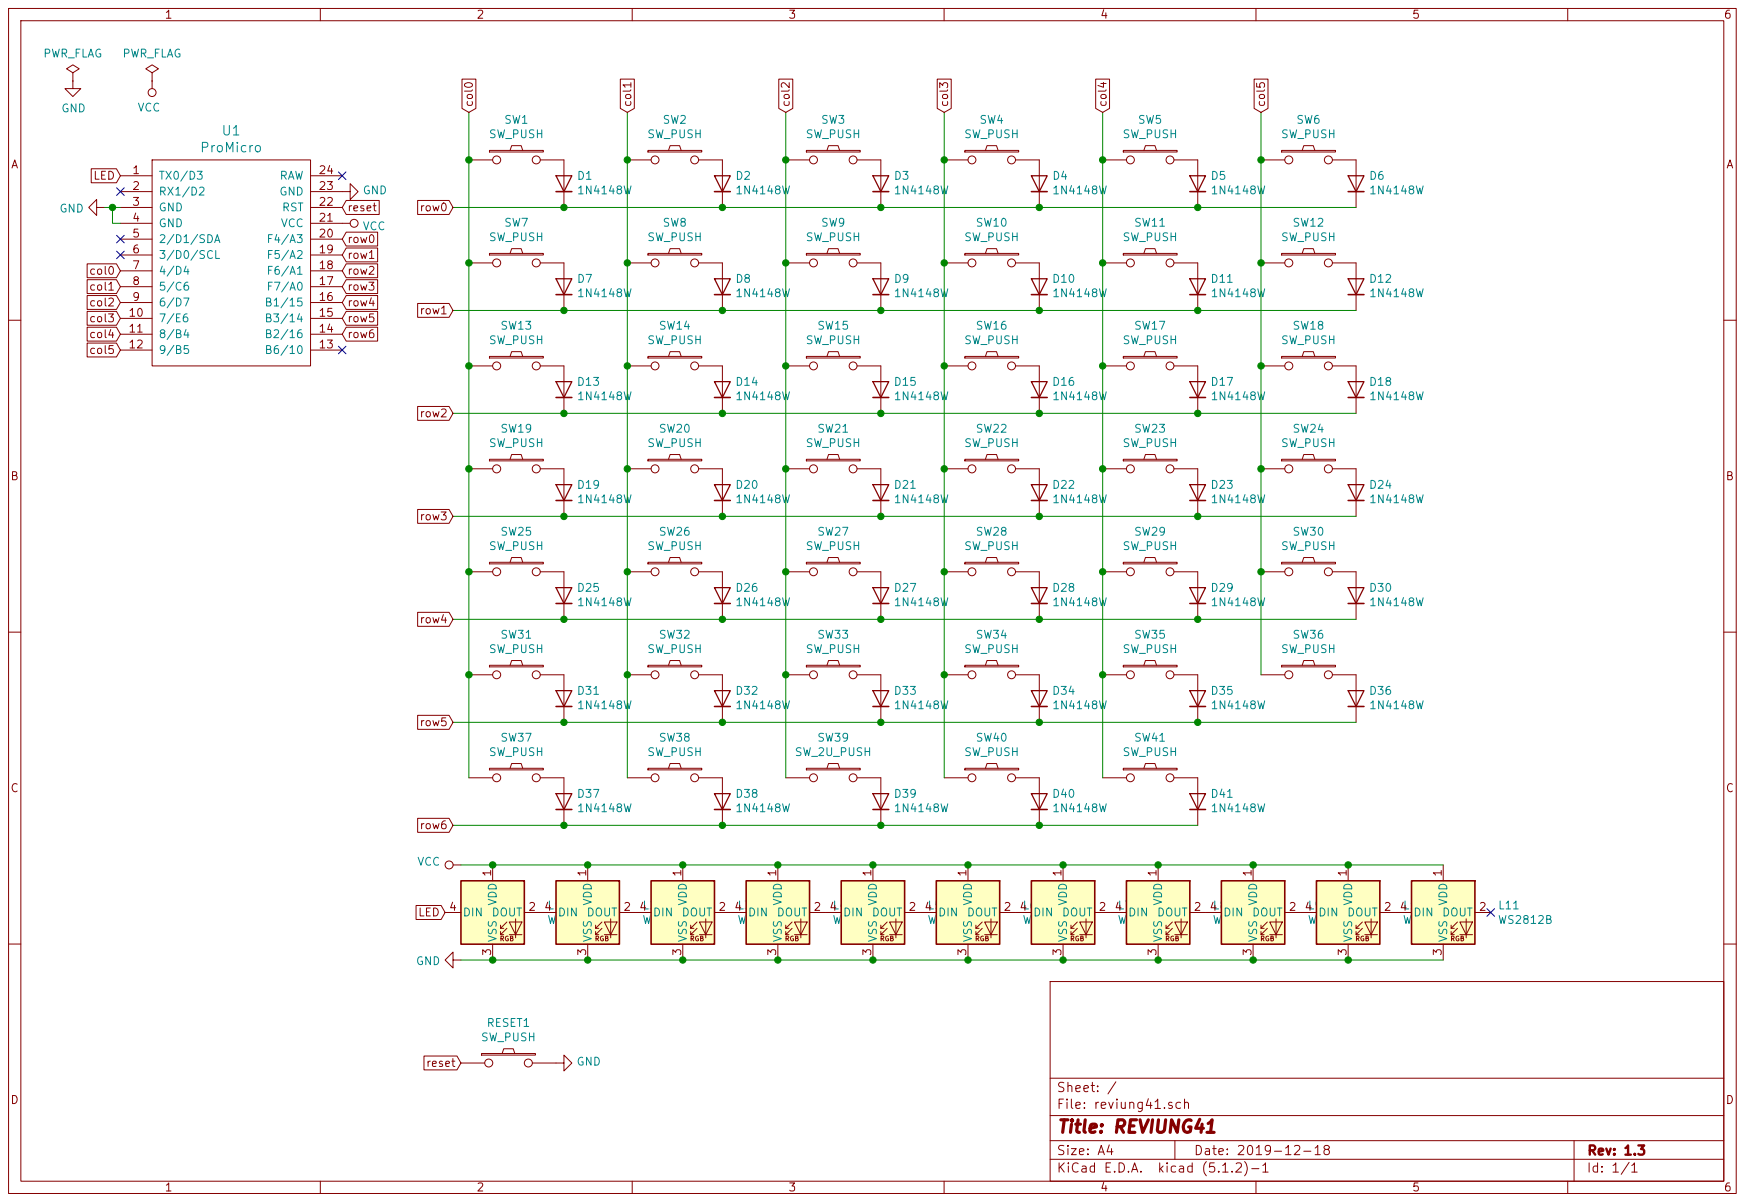
[picture p111: page 1]
