gtips/reviung/reviung41/pcb-top-plate/ver1.2/circuit_diagram.pdf

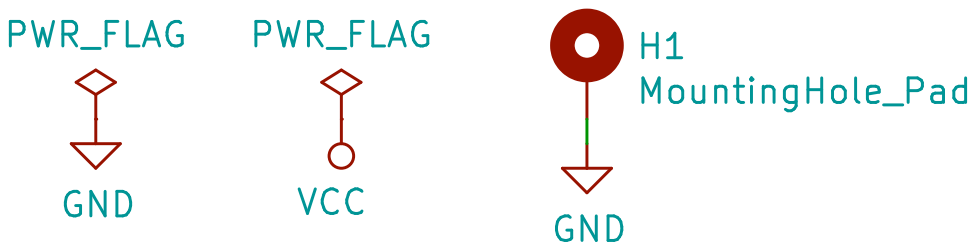
[picture p112: page 1]
