gtips/reviung/reviung41/pcb/ver1.2/circuit_diagram.pdf

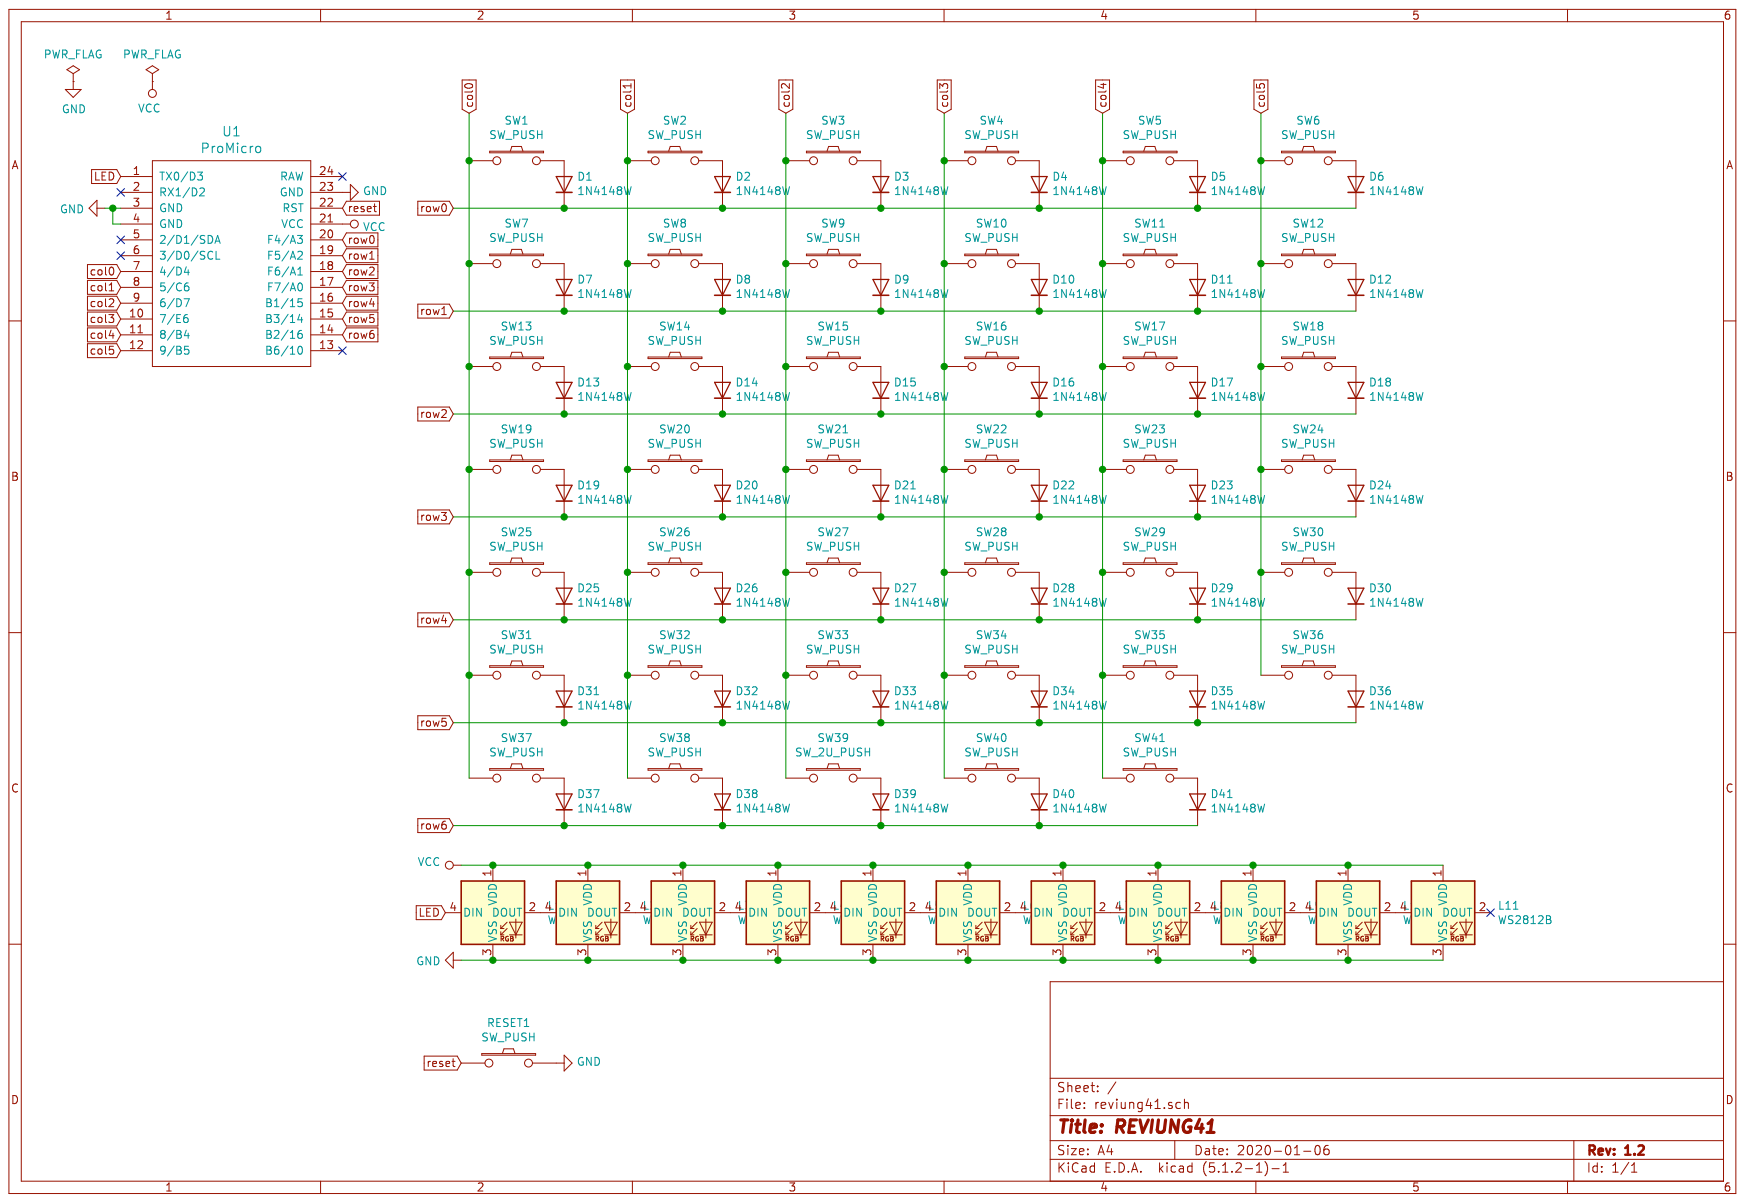
[picture p113: page 1]
