gtips/reviung/reviung34/acrylic-plate/bottom-plate/ver1.0/reviung34-bottom-plate-2mm-ver1.pdf

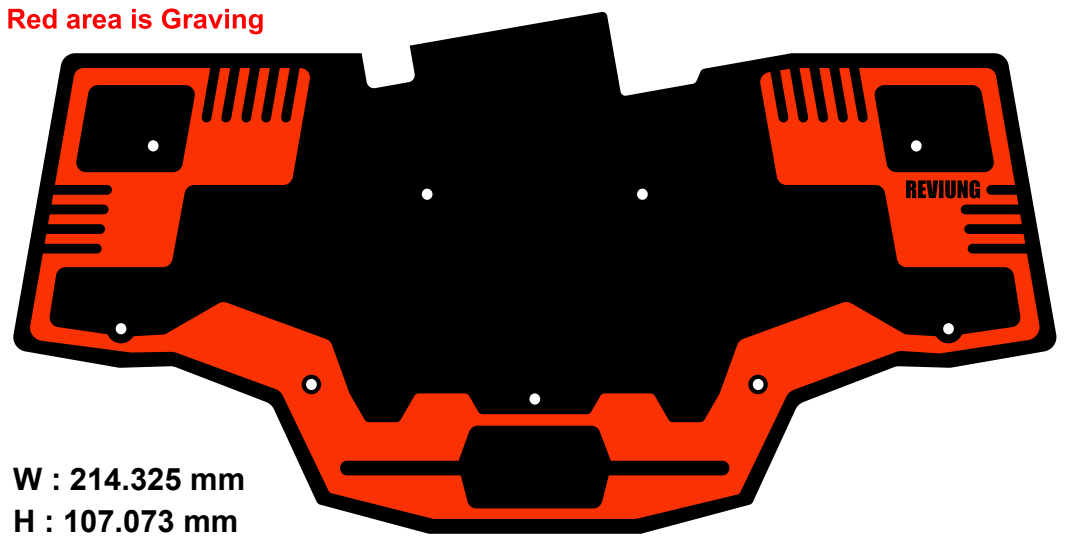
[picture p114: page 1]
