gtips/reviung/reviung34/acrylic-plate/lower-middle-plate/ver1.0/r34-lower-middle-3mm-ver1-TP.pdf

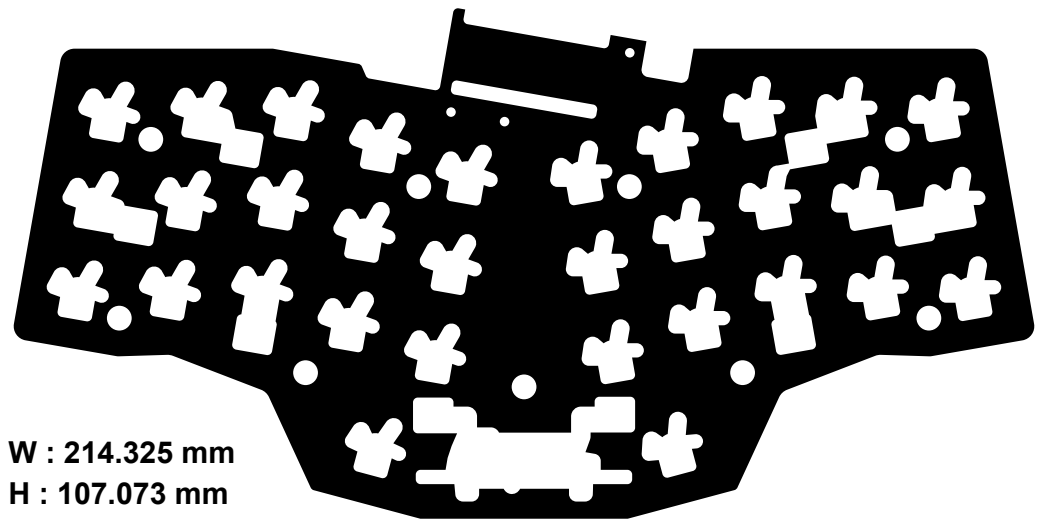
[picture p115: page 1]
