gtips/reviung/reviung39_Mk-II/acrylic-plate/bottom-plate/ver1.2/reviung39MkII-bottom-plate-2mm-ver1.2.pdf

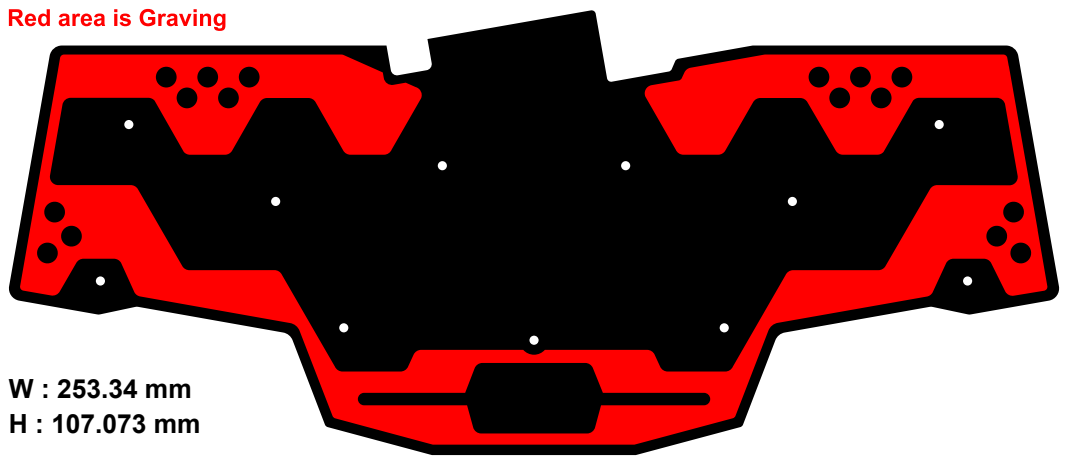
[picture p116: page 1]
