gtips/reviung/reviung41/acrylic-plate/upper-middle-plate/ver1.0/reviung41-upper-middle-plate.pdf

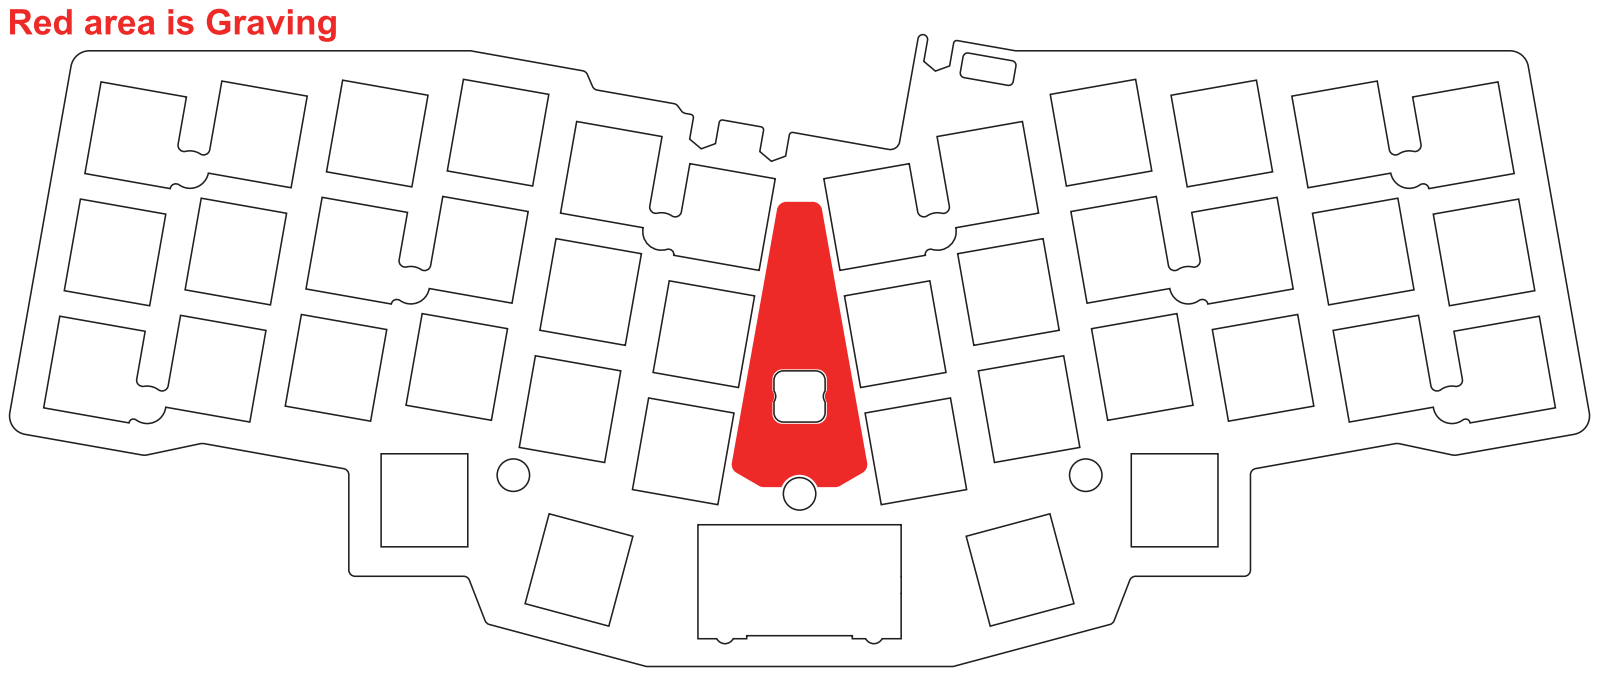
[picture p117: page 1]
