gtips/reviung/reviung41/acrylic-plate/bottom-plate/ver1.0/reviung41-bottom-plate.pdf

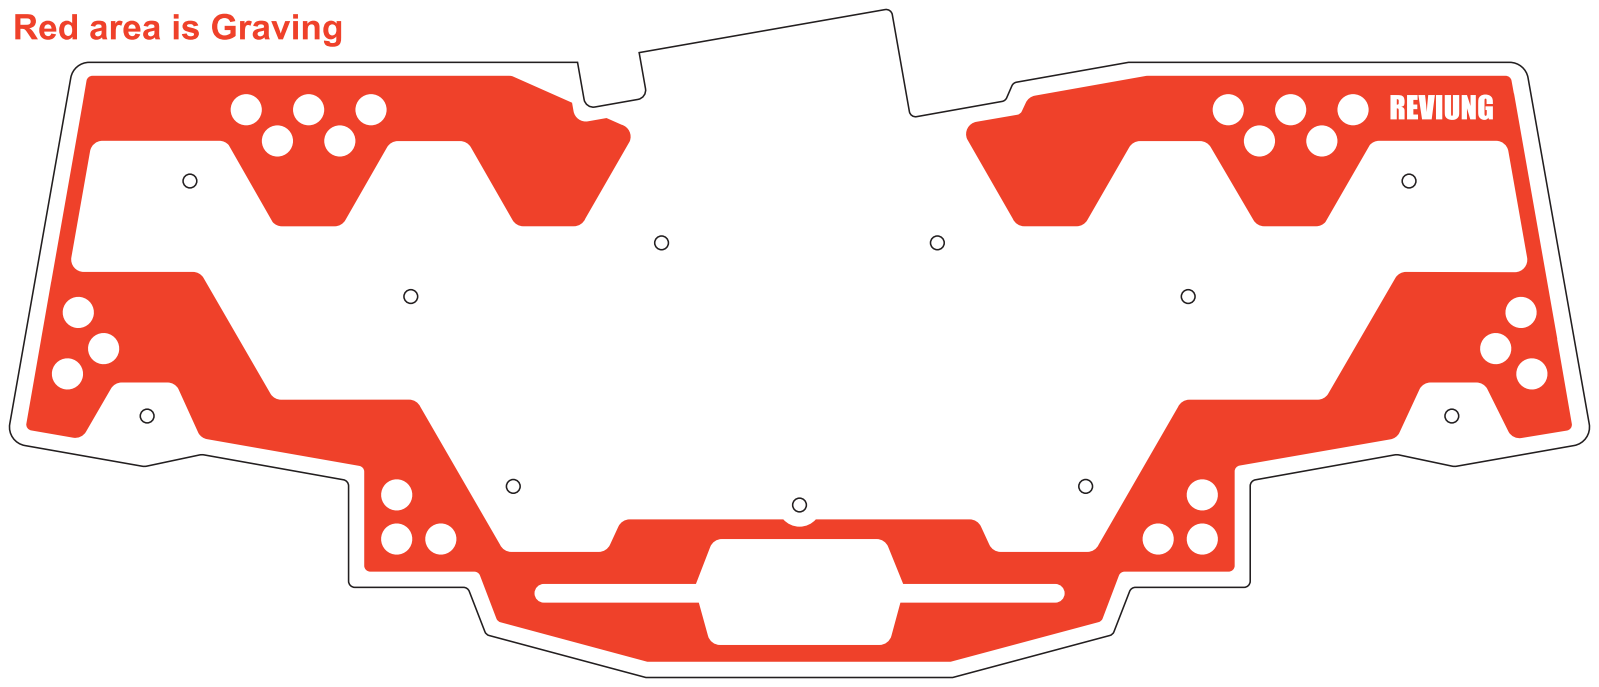
[picture p118: page 1]
