gtips/reviung/reviung41/acrylic-plate/lower-middle-plate/ver1.0/reviung41-lower-middle-plate.pdf

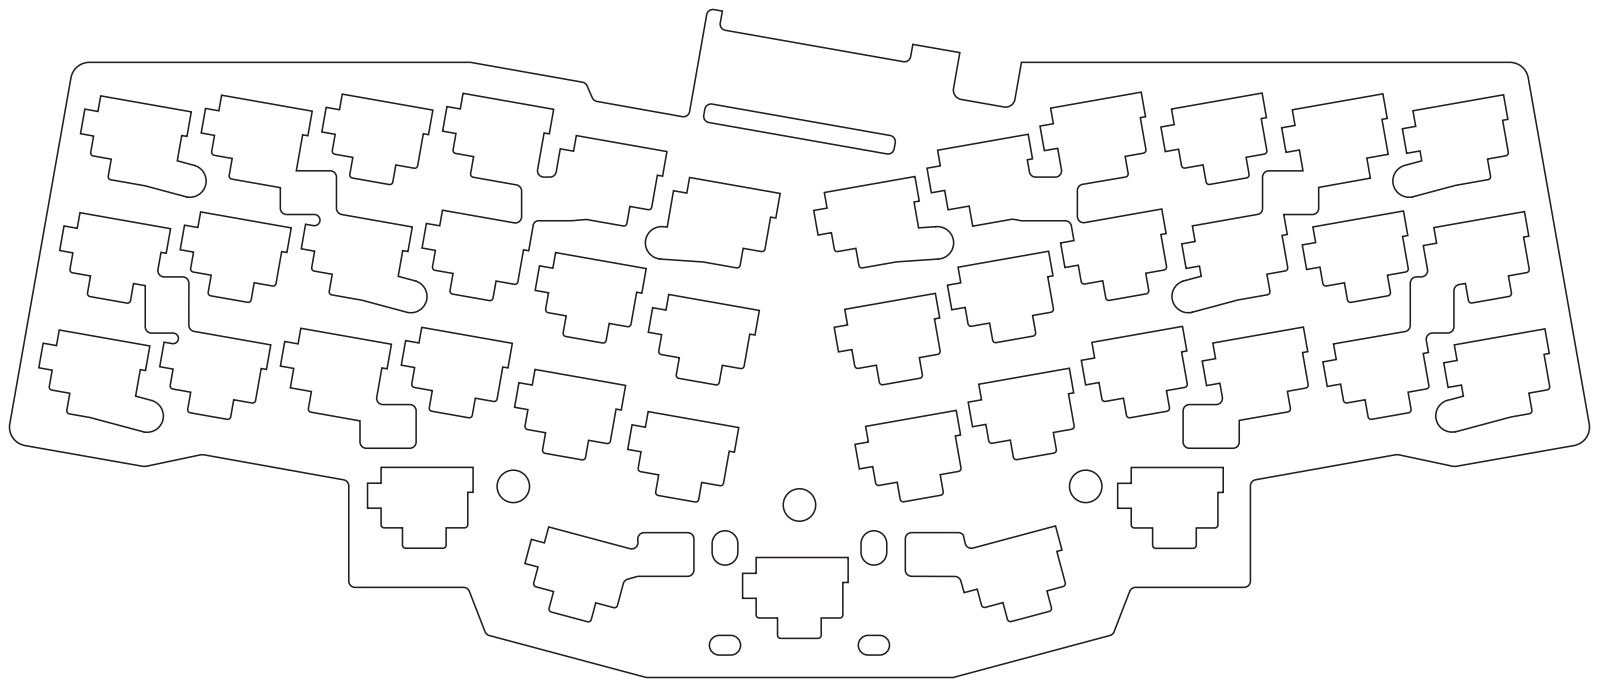
[picture p119: page 1]
