gtips/reviung/reviung34/acrylic-plate/upper-middle-plate/for-opaque/ver1.0/r34-upper-middle-3mm-ver1-OP.pdf

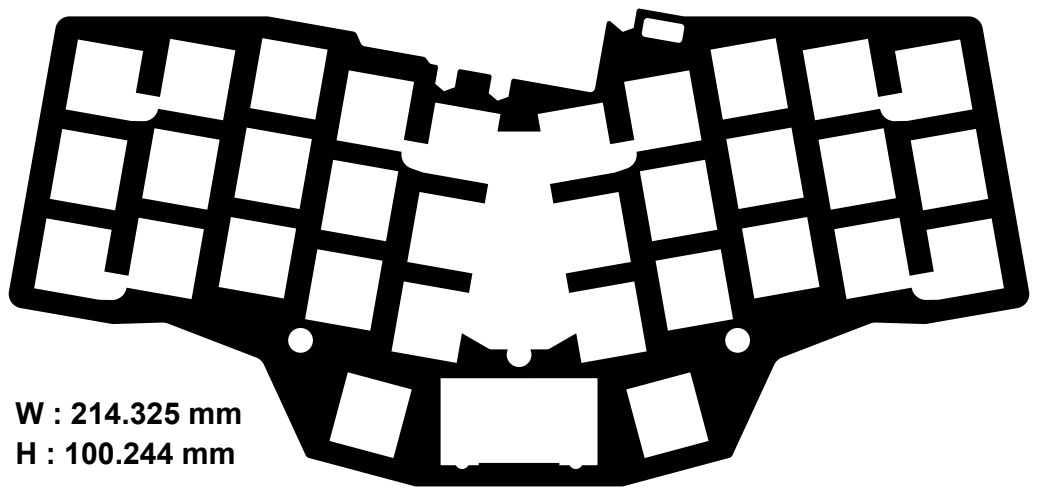
[picture p120: page 1]
