gtips/reviung/reviung34/acrylic-plate/upper-middle-plate/for-transparent/ver1.0/r34-upper-middle-3mm-ver1-TP.pdf

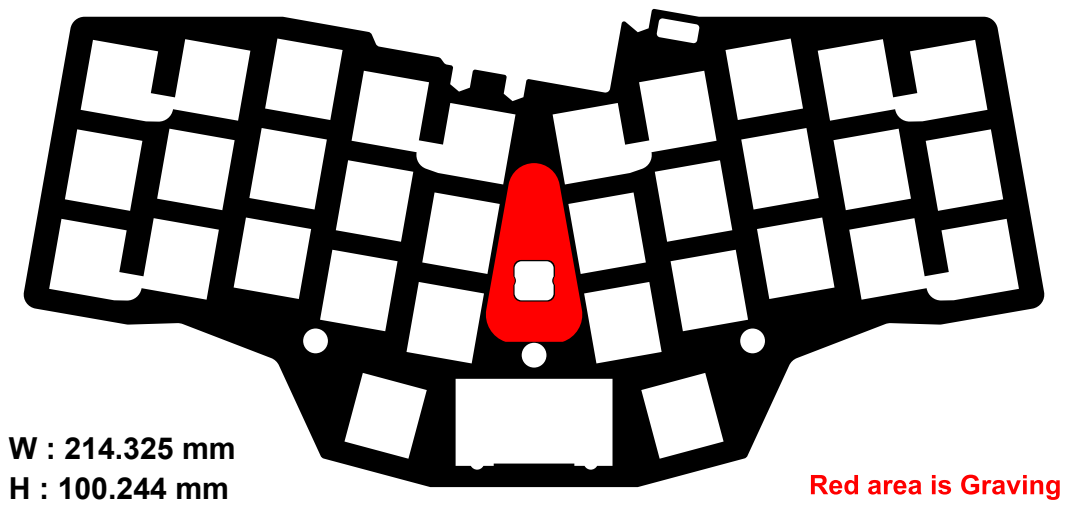
[picture p121: page 1]
