gtips/reviung/reviung39_Mk-II/acrylic-plate/lower-middle-plate/for-opaque/ver1.1/r39mkII-lower-middle-3mm-ver1.1-OP.pdf

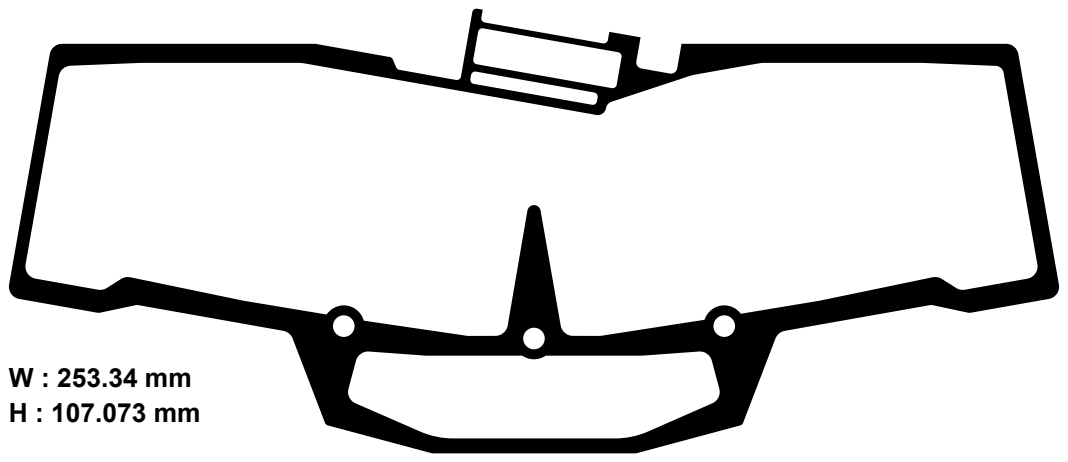
[picture p122: page 1]
