gtips/reviung/reviung39_Mk-II/acrylic-plate/lower-middle-plate/for-transparent/ver1.1/r39mkII-lower-middle-3mm-ver1.1-TP.pdf

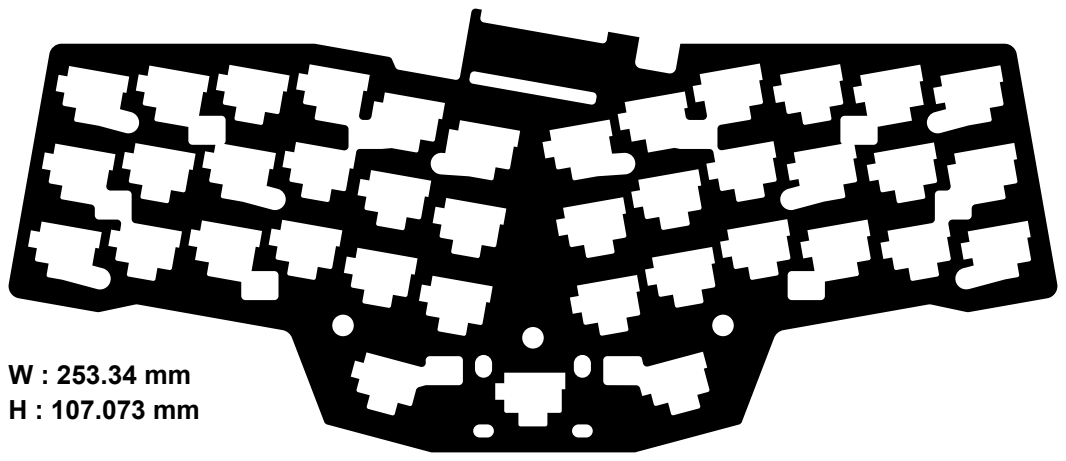
[picture p123: page 1]
