gtips/reviung/reviung39_Mk-II/acrylic-plate/upper-middle-plate/for-opaque/ver1.0/r39mkII-upper-middle-3mm-ver1.0-OP.pdf

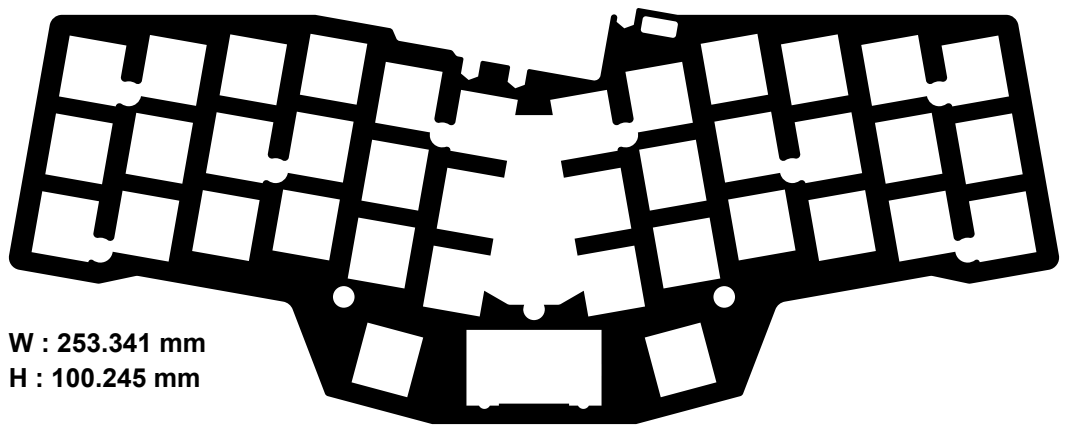
[picture p124: page 1]
