gtips/reviung/reviung39_Mk-II/acrylic-plate/upper-middle-plate/for-transparent/ver1.0/r39mkII-upper-middle-3mm-ver1.0-TP.pdf

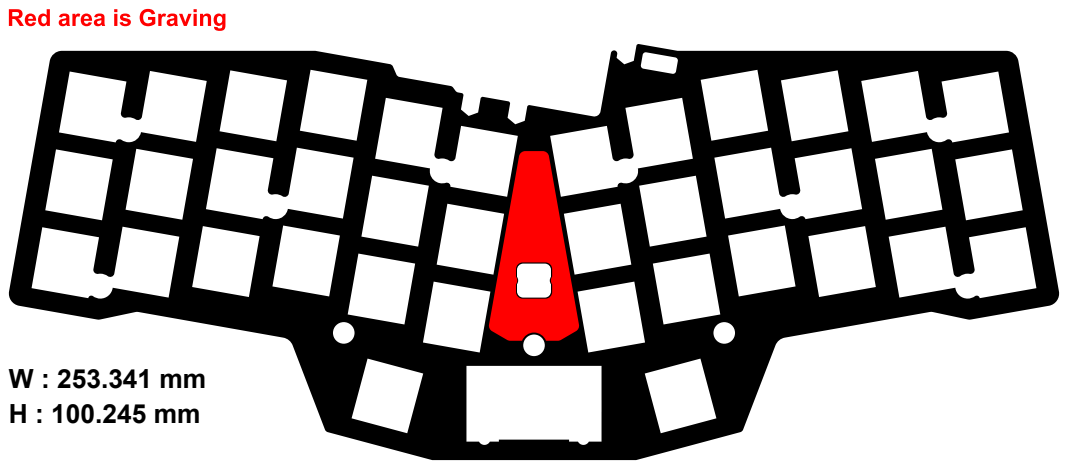
[picture p125: page 1]
